DinethraDivanjana2001/TechBots-STM-based-Bot-Working/Raspberry Pi firmware/Edge detection/input_image.jpeg

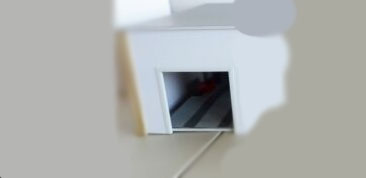
Raspberry Pi firmware/Edge detection/input_image.jpeg
