DinethraDivanjana2001/TechBots-STM-based-Bot-Working/3D designs/slrc 3D assembly blender/Assem1.STEP - Motor Assembly.STEP-1 65mm Wheel_默认.STEP-1 蓝色轮毂_默认.STEP-1.STL

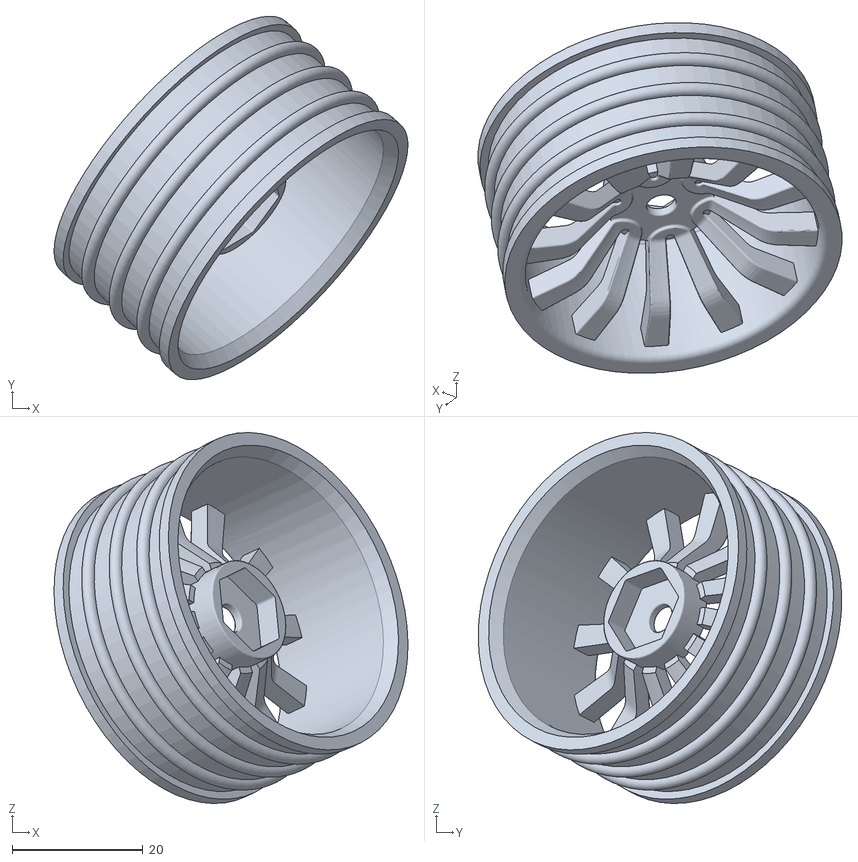
[picture p23: CAD file, 2024-07-25]
3D designs/slrc 3D assembly blender/Assem1.STEP - Motor Assembly.STEP-1 65mm Wheel_默认.STEP-1 蓝色轮毂_默认.STEP-1.STL
54.2 x 55.7 x 56.8
