DinethraDivanjana2001/TechBots-STM-based-Bot-Working/3D designs/slrc 3D assembly blender/Assem1.STEP - Motor Assembly.STEP-1 65mm Wheel_默认.STEP-1 3MM联轴器_默认.STEP-1.STL

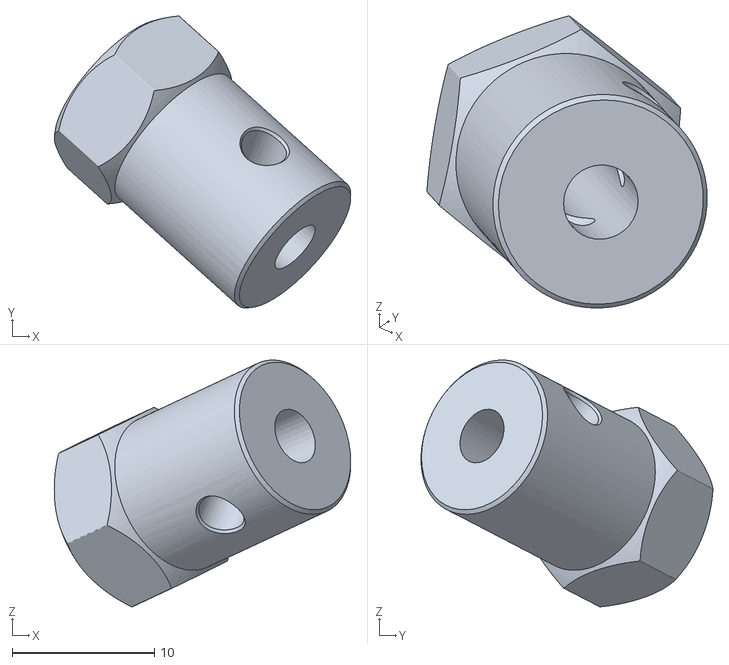
[picture p25: CAD file, 2024-07-25]
3D designs/slrc 3D assembly blender/Assem1.STEP - Motor Assembly.STEP-1 65mm Wheel_默认.STEP-1 3MM联轴器_默认.STEP-1.STL
20.9 x 20.6 x 17.4
