DinethraDivanjana2001/TechBots-STM-based-Bot-Working/3D designs/slrc 3D assembly blender/Assem1.STEP - Full  Arm Assembly.STEP-1 RDS3225 v7.STEP-2 RDS3225 v7_3^RDS3225 v7.STEP-1 RDS3225-0_3^RDS3225 v7_3_RDS3225 v7.STEP-1.STL

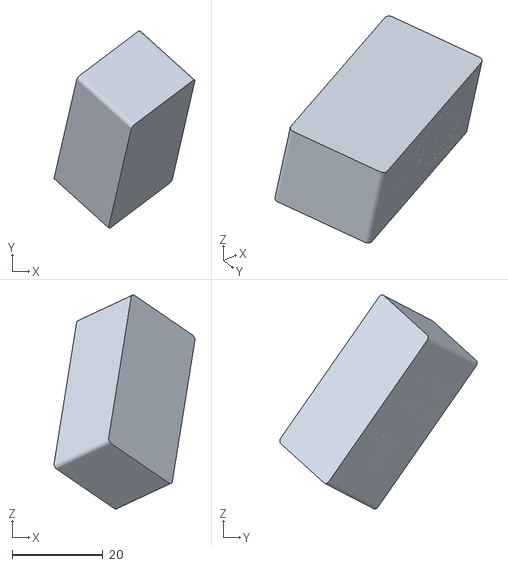
[picture p26: CAD file, 2024-07-25]
3D designs/slrc 3D assembly blender/Assem1.STEP - Full Arm Assembly.STEP-1 RDS3225 v7.STEP-2 RDS3225 v7_3^RDS3225 v7.STEP-1 RDS3225-0_3^RDS3225 v7_3_RDS3225 v7.STEP-1.STL
31.0 x 43.4 x 47.1
