DinethraDivanjana2001/TechBots-STM-based-Bot-Working/3D designs/slrc 3D assembly blender/Assem1.STEP - Full  Arm Assembly.STEP-1 Arm gripper new.STEP-2.STL

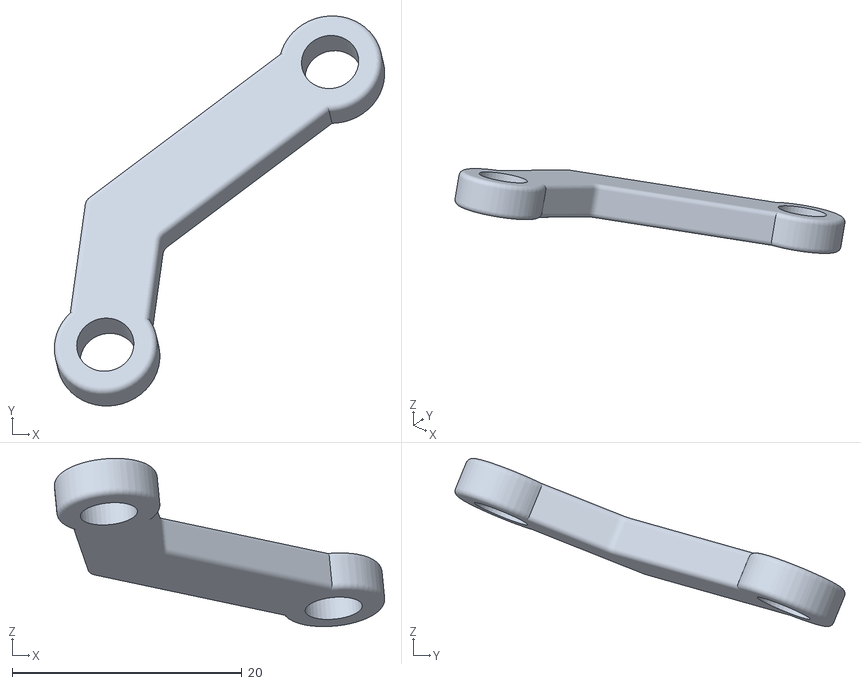
[picture p27: CAD file, 2024-07-25]
3D designs/slrc 3D assembly blender/Assem1.STEP - Full Arm Assembly.STEP-1 Arm gripper new.STEP-2.STL
28.7 x 33.9 x 14.6
