DinethraDivanjana2001/TechBots-STM-based-Bot-Working/3D designs/slrc 3D assembly blender/Assem1.STEP - Motor Assembly.STEP-1 metal-gearmotor-bracket.STEP-1.STL

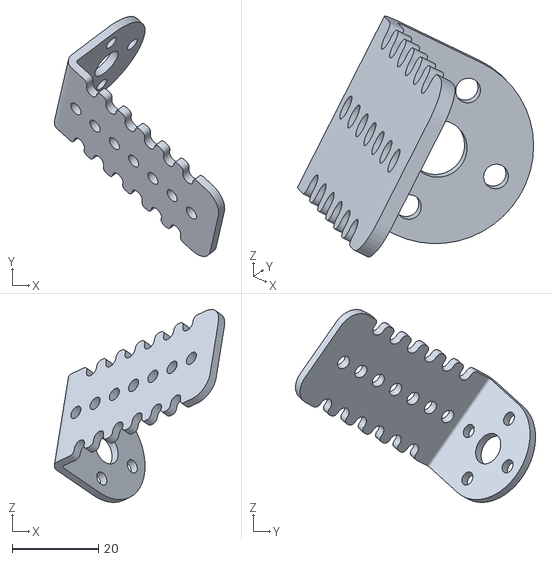
[picture p28: CAD file, 2024-07-25]
3D designs/slrc 3D assembly blender/Assem1.STEP - Motor Assembly.STEP-1 metal-gearmotor-bracket.STEP-1.STL
39.4 x 55.5 x 44.6
