DinethraDivanjana2001/TechBots-STM-based-Bot-Working/3D designs/slrc 3D assembly blender/Assem1.STEP - Motor Assembly.STEP-1 25d-metal-gearmotor-34-47-encoder.step.STEP-1 25d-metal-gearmotor-34-47-encoder2.step.STEP-1.STL

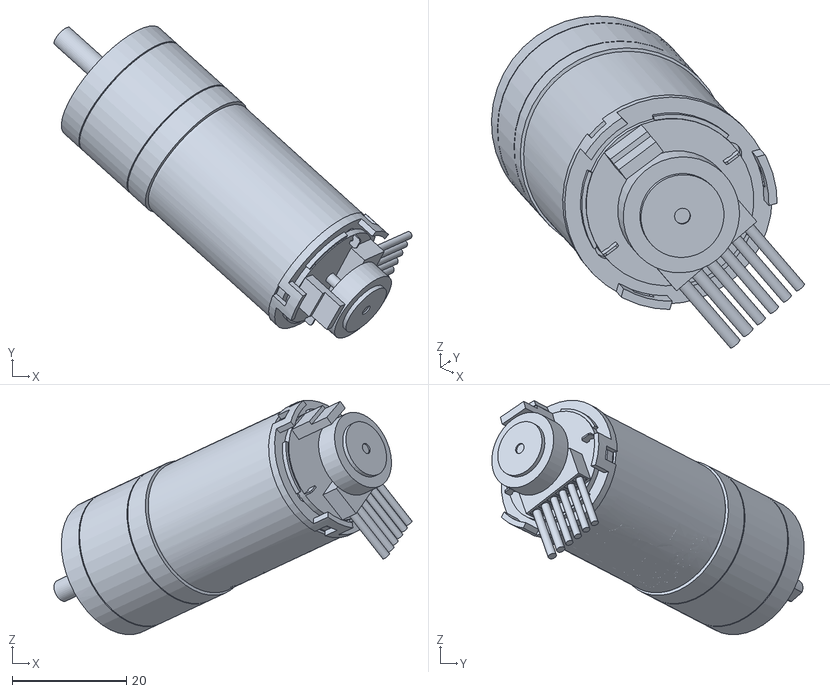
[picture p29: CAD file, 2024-07-25]
3D designs/slrc 3D assembly blender/Assem1.STEP - Motor Assembly.STEP-1 25d-metal-gearmotor-34-47-encoder.step.STEP-1 25d-metal-gearmotor-34-47-encoder2.step.STEP-1.STL
62.8 x 54.7 x 41.0
