DinethraDivanjana2001/TechBots-STM-based-Bot-Working/3D designs/slrc 3D assembly blender/Assem1.STEP - Tof assembly.STEP-1 vl53l0x.STEP-1 pin_header.STEP-6.STL

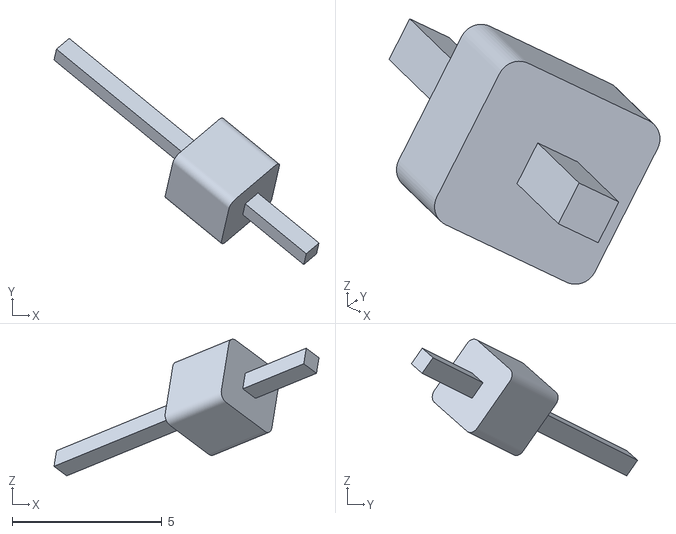
[picture p30: CAD file, 2024-07-25]
3D designs/slrc 3D assembly blender/Assem1.STEP - Tof assembly.STEP-1 vl53l0x.STEP-1 pin_header.STEP-6.STL
8.84 x 7.55 x 4.56
