DinethraDivanjana2001/TechBots-STM-based-Bot-Working/3D designs/slrc 3D assembly blender/Assem1.STEP - Tof assembly.STEP-1 vl53l0x.STEP-1 vl53l0x_PCB.STEP-1.STL

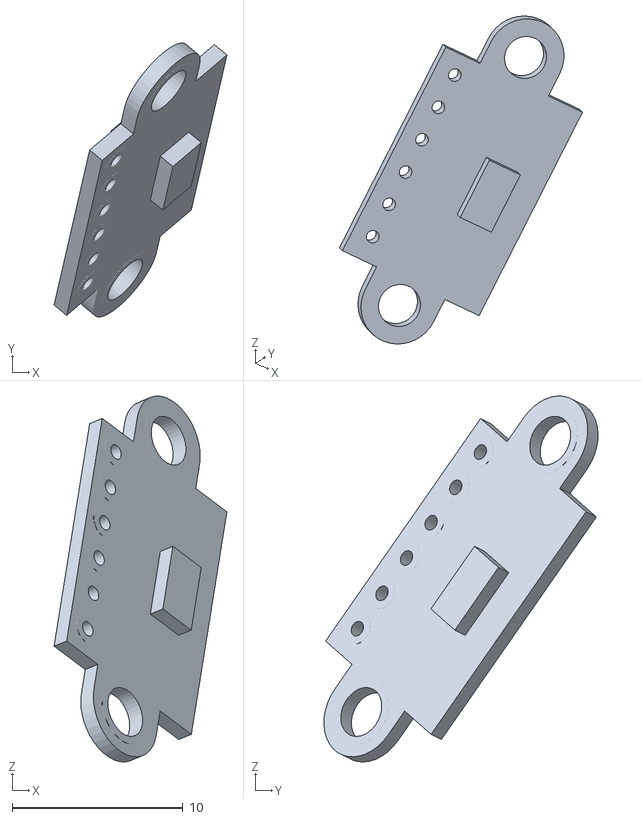
[picture p31: CAD file, 2024-07-25]
3D designs/slrc 3D assembly blender/Assem1.STEP - Tof assembly.STEP-1 vl53l0x.STEP-1 vl53l0x_PCB.STEP-1.STL
10.1 x 16.0 x 21.4
