DinethraDivanjana2001/TechBots-STM-based-Bot-Working/3D designs/slrc 3D assembly blender/Assem1.STEP - Full  Arm Assembly.STEP-1 RDS3225 v7.STEP-1 RDS3225 v7_3^RDS3225 v7.STEP-1 RDS3225-1_3^RDS3225 v7_3_RDS3225 v7.STEP-1.STL

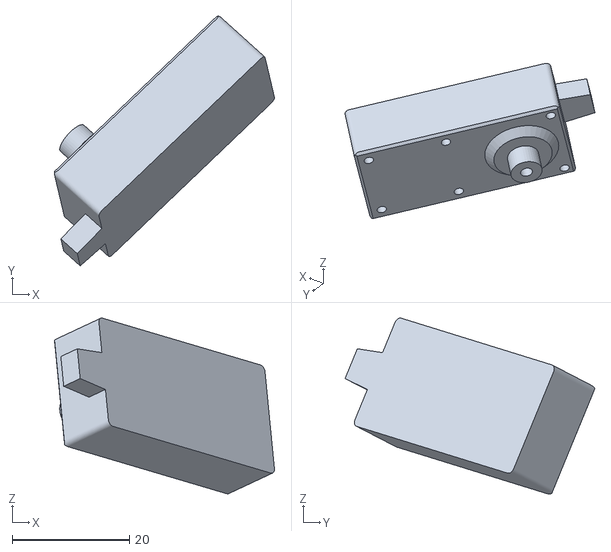
[picture p34: CAD file, 2024-07-25]
3D designs/slrc 3D assembly blender/Assem1.STEP - Full Arm Assembly.STEP-1 RDS3225 v7.STEP-1 RDS3225 v7_3^RDS3225 v7.STEP-1 RDS3225-1_3^RDS3225 v7_3_RDS3225 v7.STEP-1.STL
37.5 x 42.5 x 29.9
