DinethraDivanjana2001/TechBots-STM-based-Bot-Working/3D designs/slrc 3D assembly blender/Assem1.STEP - Full  Arm Assembly.STEP-1 RDS3225 v7.STEP-1 RDS3225 v7_3^RDS3225 v7.STEP-1 RDS3225-0_3^RDS3225 v7_3_RDS3225 v7.STEP-1.STL

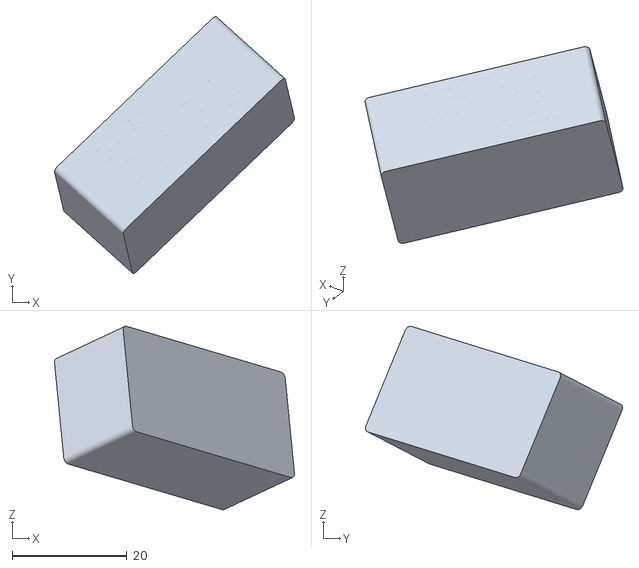
[picture p35: CAD file, 2024-07-25]
3D designs/slrc 3D assembly blender/Assem1.STEP - Full Arm Assembly.STEP-1 RDS3225 v7.STEP-1 RDS3225 v7_3^RDS3225 v7.STEP-1 RDS3225-0_3^RDS3225 v7_3_RDS3225 v7.STEP-1.STL
41.9 x 44.9 x 32.0
