DinethraDivanjana2001/TechBots-STM-based-Bot-Working/3D designs/slrc 3D assembly blender/Assem1.STEP - Tof assembly.STEP-2 New tof mount.STEP-1.STL

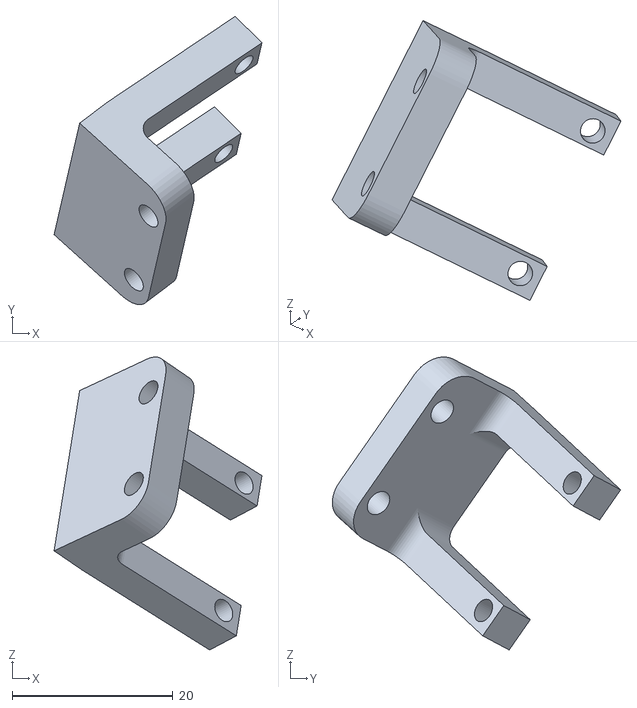
[picture p38: CAD file, 2024-07-25]
3D designs/slrc 3D assembly blender/Assem1.STEP - Tof assembly.STEP-2 New tof mount.STEP-1.STL
25.9 x 35.9 x 36.5
