DinethraDivanjana2001/TechBots-STM-based-Bot-Working/3D designs/slrc 3D assembly blender/Assem1.STEP - Full  Arm Assembly.STEP-1 proximity tl-w5mc1_Valor predeterminado.STEP-1.STL

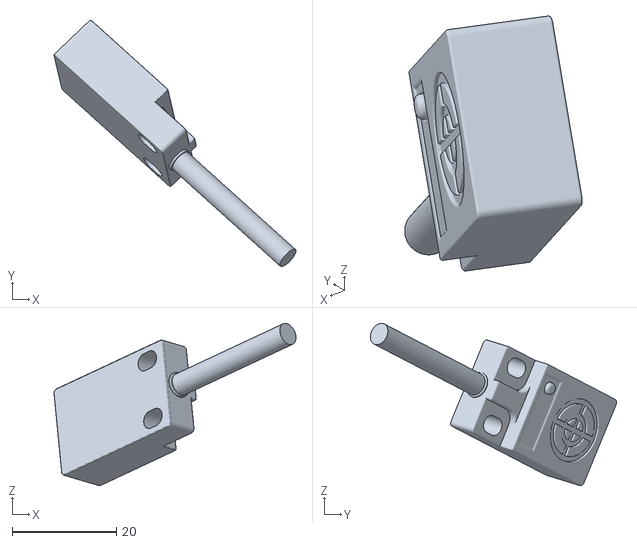
[picture p40: CAD file, 2024-07-25]
3D designs/slrc 3D assembly blender/Assem1.STEP - Full Arm Assembly.STEP-1 proximity tl-w5mc1_Valor predeterminado.STEP-1.STL
46.5 x 47.3 x 31.2
