DinethraDivanjana2001/TechBots-STM-based-Bot-Working/3D designs/slrc 3D assembly blender/Assem1.STEP - Full  Arm Assembly.STEP-1 Jaw plate flip new.STEP-1.STL

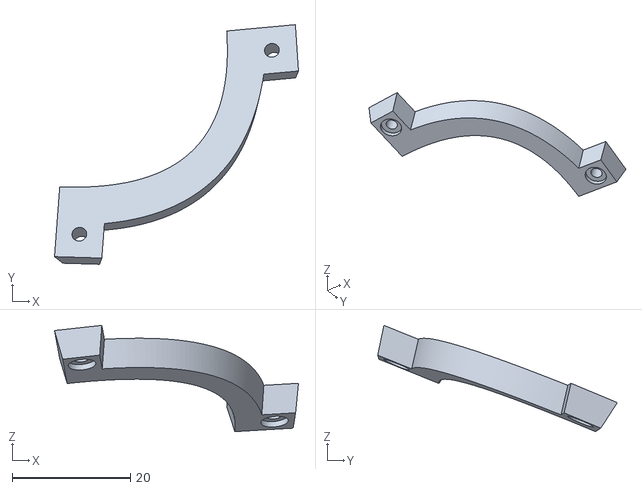
[picture p42: CAD file, 2024-07-25]
3D designs/slrc 3D assembly blender/Assem1.STEP - Full Arm Assembly.STEP-1 Jaw plate flip new.STEP-1.STL
41.2 x 40.5 x 18.0
