DinethraDivanjana2001/TechBots-STM-based-Bot-Working/3D designs/slrc 3D assembly blender/Assem1.STEP - Motor Assembly.STEP-2 metal-gearmotor-bracket.STEP-1.STL

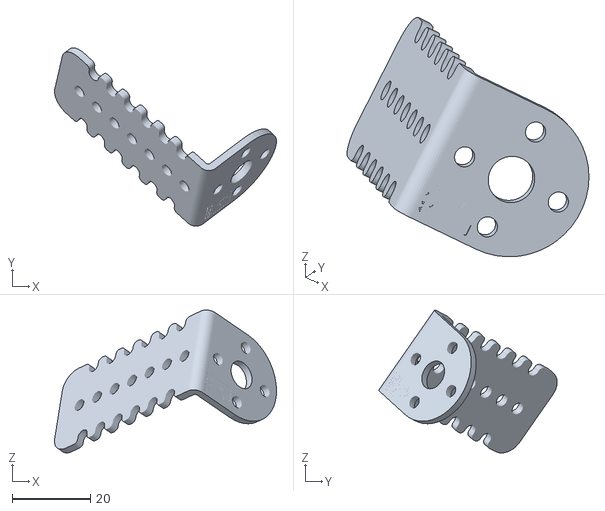
[picture p45: CAD file, 2024-07-25]
3D designs/slrc 3D assembly blender/Assem1.STEP - Motor Assembly.STEP-2 metal-gearmotor-bracket.STEP-1.STL
56.6 x 45.4 x 36.4
