DinethraDivanjana2001/TechBots-STM-based-Bot-Working/3D designs/slrc 3D assembly blender/Assem1.STEP - Motor Assembly.STEP-2 25d-metal-gearmotor-34-47-encoder.step.STEP-1 25d-metal-gearmotor-34-47-encoder2.step.STEP-1.STL

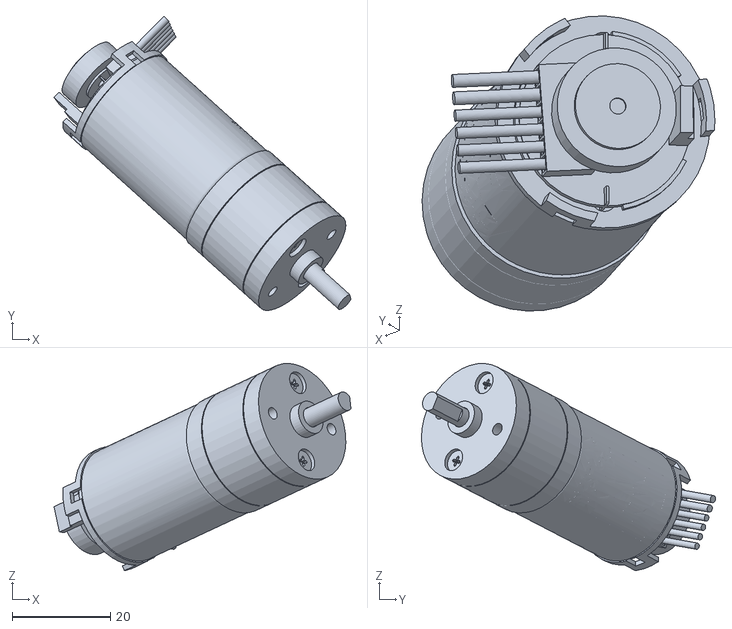
[picture p47: CAD file, 2024-07-25]
3D designs/slrc 3D assembly blender/Assem1.STEP - Motor Assembly.STEP-2 25d-metal-gearmotor-34-47-encoder.step.STEP-1 25d-metal-gearmotor-34-47-encoder2.step.STEP-1.STL
60.6 x 60.0 x 42.3
