DinethraDivanjana2001/TechBots-STM-based-Bot-Working/3D designs/slrc 3D assembly blender/Assem1.STEP - Motor Assembly.STEP-2 25d-metal-gearmotor-34-47-encoder.step.STEP-1 25d-metal-gearmotor-34-47-encoder1.step.STEP-1.STL

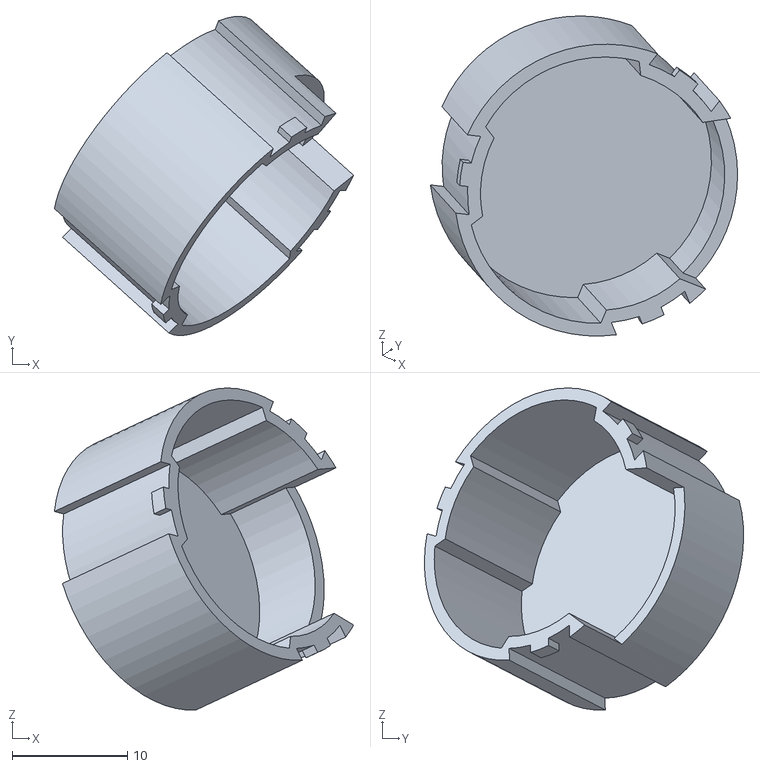
[picture p48: CAD file, 2024-07-25]
3D designs/slrc 3D assembly blender/Assem1.STEP - Motor Assembly.STEP-2 25d-metal-gearmotor-34-47-encoder.step.STEP-1 25d-metal-gearmotor-34-47-encoder1.step.STEP-1.STL
25.9 x 27.7 x 27.9
