DinethraDivanjana2001/TechBots-STM-based-Bot-Working/3D designs/slrc 3D assembly blender/Assem1.STEP - Motor Assembly.STEP-1 25d-metal-gearmotor-34-47-encoder.step.STEP-1 25d-metal-gearmotor-34-47-encoder1.step.STEP-1.STL

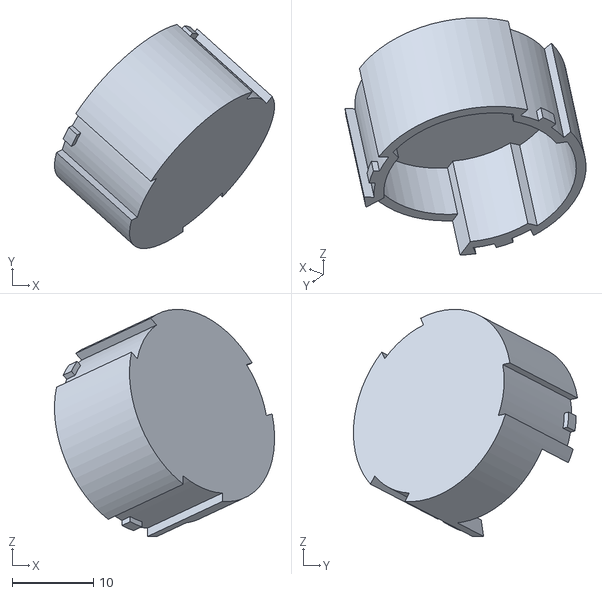
[picture p49: CAD file, 2024-07-25]
3D designs/slrc 3D assembly blender/Assem1.STEP - Motor Assembly.STEP-1 25d-metal-gearmotor-34-47-encoder.step.STEP-1 25d-metal-gearmotor-34-47-encoder1.step.STEP-1.STL
27.0 x 27.5 x 27.9
