DinethraDivanjana2001/TechBots-STM-based-Bot-Working/3D designs/slrc 3D assembly blender/Assem1.STEP - vl53l0x.STEP-2 pin_header.STEP-4.STL

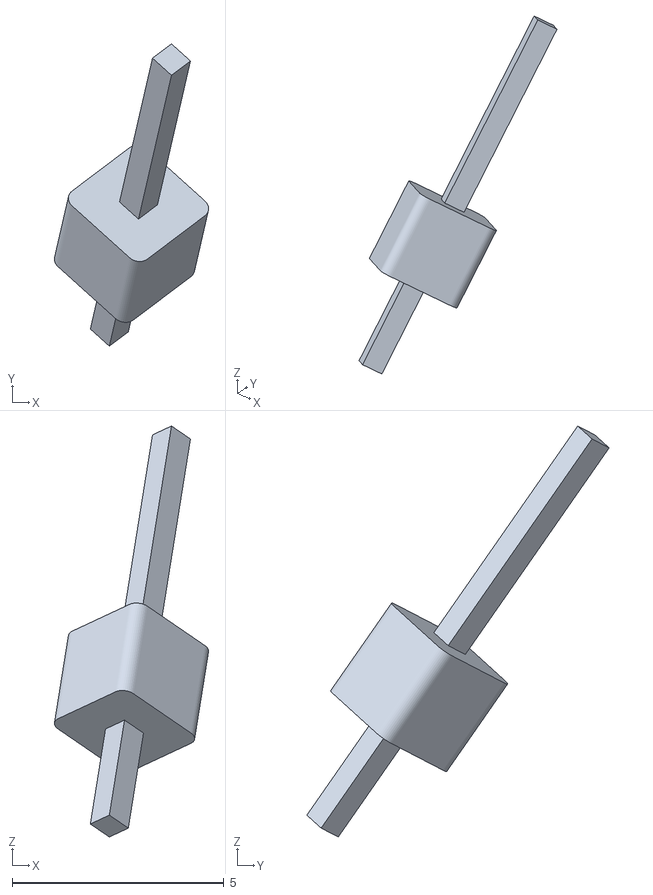
[picture p52: CAD file, 2024-07-25]
3D designs/slrc 3D assembly blender/Assem1.STEP - vl53l0x.STEP-2 pin_header.STEP-4.STL
3.65 x 7.14 x 9.71
