DinethraDivanjana2001/TechBots-STM-based-Bot-Working/Shooter/Solid_works_design/Wheel.SLDPRT

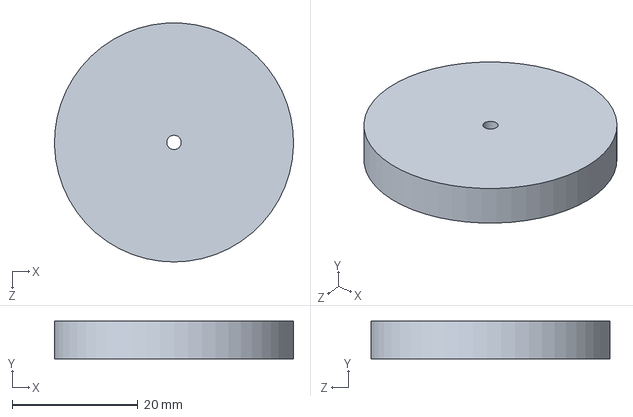
[picture p53: CAD file, 2024-07-25]
Shooter/Solid_works_design/Wheel.SLDPRT
38.0 x 6.00 x 38.0 mm
