DinethraDivanjana2001/TechBots-STM-based-Bot-Working/Shooter/Solid_works_design/rs380 motor.step.SLDPRT

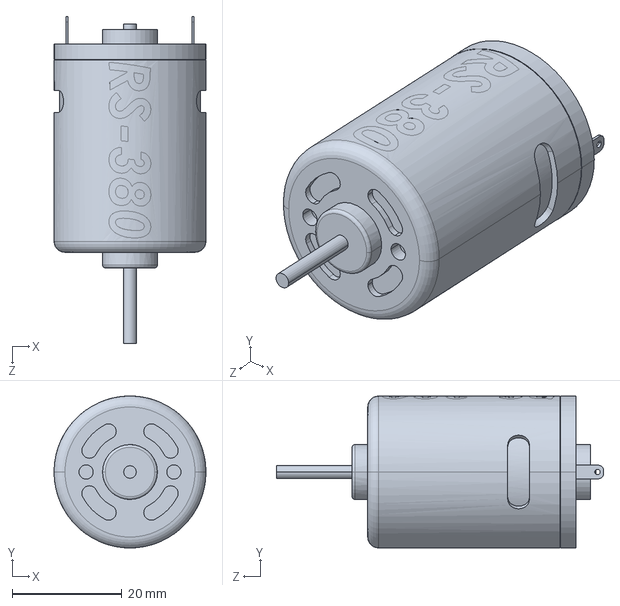
[picture p54: CAD file, 2024-07-25]
Shooter/Solid_works_design/rs380 motor.step.SLDPRT
27.7 x 27.7 x 59.7 mm
