DinethraDivanjana2001/TechBots-STM-based-Bot-Working/Shooter/Solid_works_design/Shooter.SLDPRT

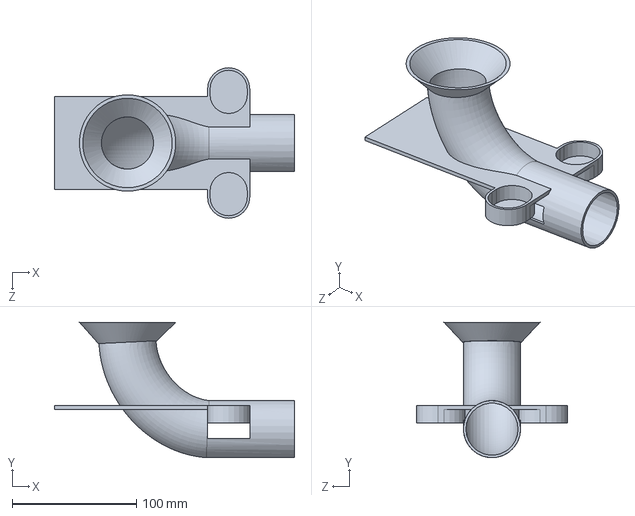
[picture p55: CAD file, 2024-07-25]
Shooter/Solid_works_design/Shooter.SLDPRT
193.2 x 109.0 x 121.2 mm
