DinethraDivanjana2001/TechBots-STM-based-Bot-Working/3D designs/slrc 3D assembly blender/Assem1.STEP - caster ball wheel.STEP-1.STL

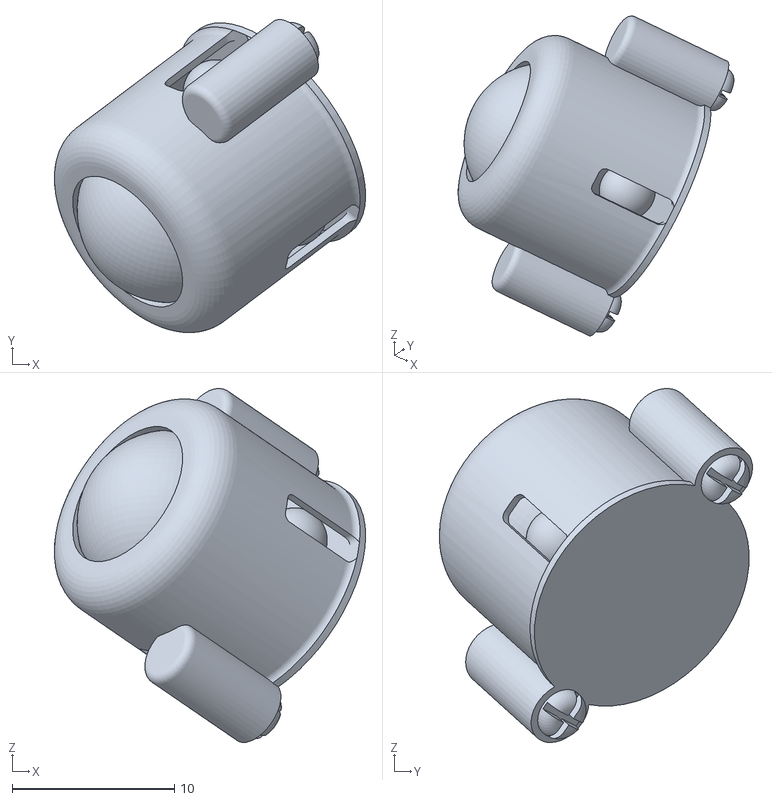
[picture p56: CAD file, 2024-07-25]
3D designs/slrc 3D assembly blender/Assem1.STEP - caster ball wheel.STEP-1.STL
19.2 x 19.3 x 21.8
