DinethraDivanjana2001/TechBots-STM-based-Bot-Working/3D designs/slrc 3D assembly blender/Assem1.STEP - Base.STEP-1.STL

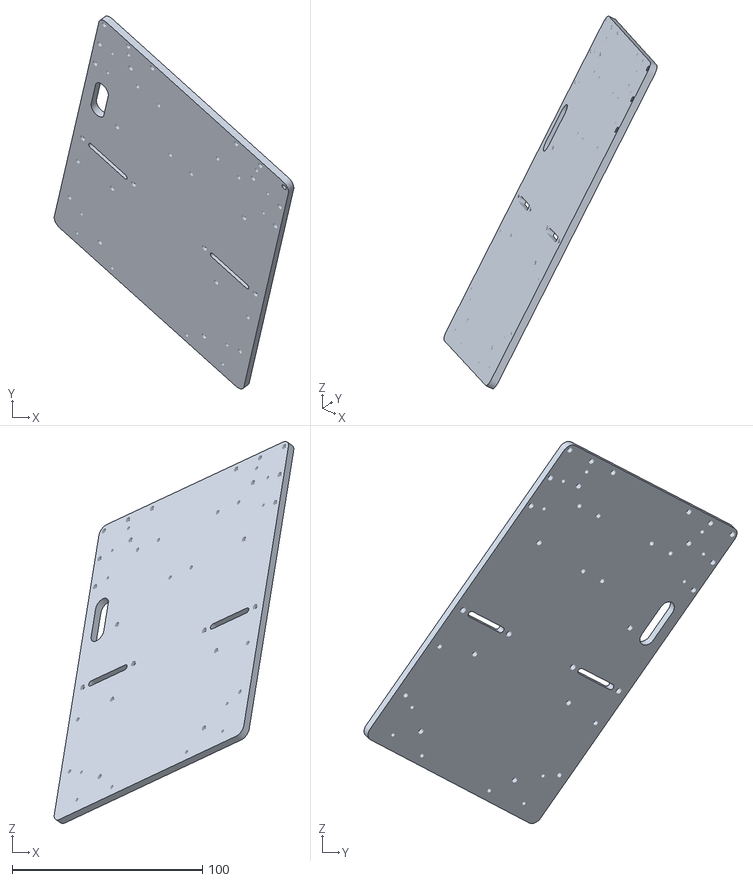
[picture p57: CAD file, 2024-07-25]
3D designs/slrc 3D assembly blender/Assem1.STEP - Base.STEP-1.STL
126.0 x 196.1 x 200.8
