DinethraDivanjana2001/TechBots-STM-based-Bot-Working/3D designs/slrc 3D assembly blender/Assem1.STEP - TCS34725 RGB sensor.step.STEP-1.STL

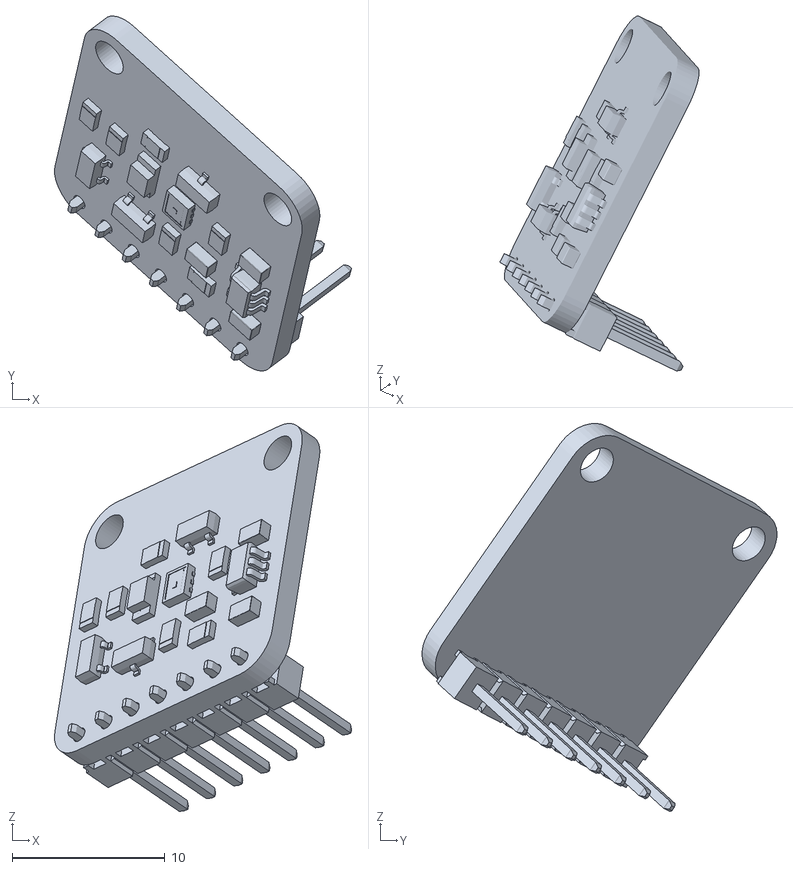
[picture p58: CAD file, 2024-07-25]
3D designs/slrc 3D assembly blender/Assem1.STEP - TCS34725 RGB sensor.step.STEP-1.STL
19.5 x 23.3 x 25.4
