DinethraDivanjana2001/TechBots-STM-based-Bot-Working/3D designs/slrc 3D assembly blender/Assem1.STEP - TFF-M3x8_DR113.step.STEP-3.STL

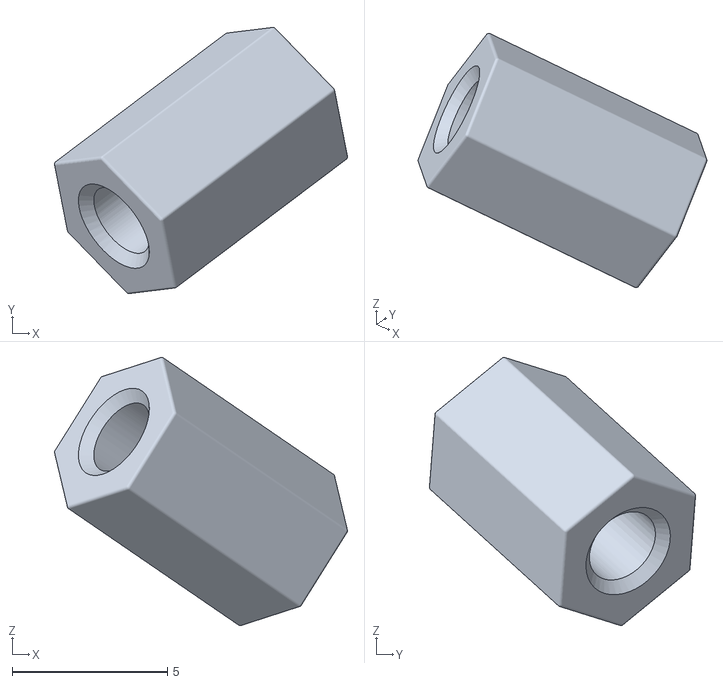
[picture p59: CAD file, 2024-07-25]
3D designs/slrc 3D assembly blender/Assem1.STEP - TFF-M3x8_DR113.step.STEP-3.STL
9.43 x 8.56 x 8.63
