DinethraDivanjana2001/TechBots-STM-based-Bot-Working/3D designs/slrc 3D assembly blender/Assem1.STEP - Stand Off 35mm_1.stp.STEP-1.STL

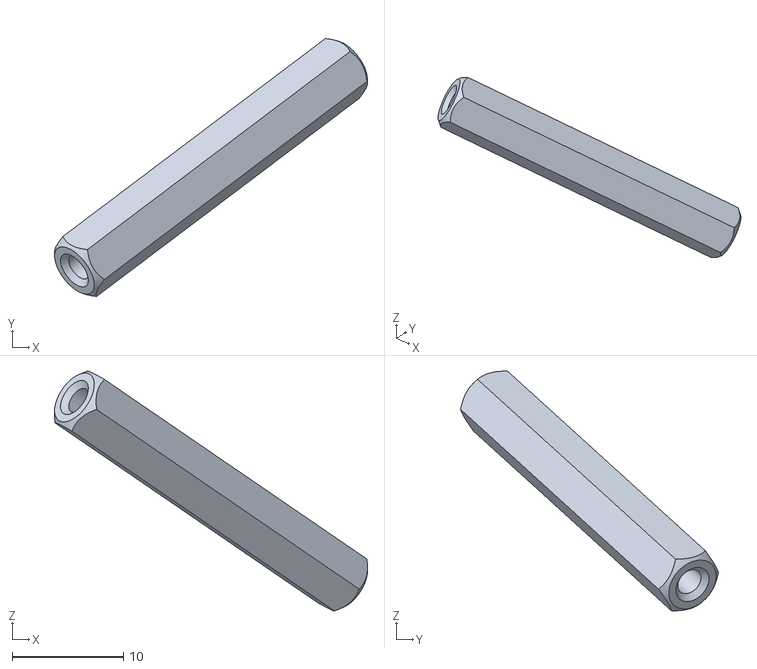
[picture p60: CAD file, 2024-07-25]
3D designs/slrc 3D assembly blender/Assem1.STEP - Stand Off 35mm_1.stp.STEP-1.STL
28.1 x 23.2 x 21.5
