DinethraDivanjana2001/TechBots-STM-based-Bot-Working/3D designs/slrc 3D assembly blender/Assem1.STEP - Turnigy_2200mAh_3S_20C_Lipo_Pack_Valor predeterminado.STEP-1.STL

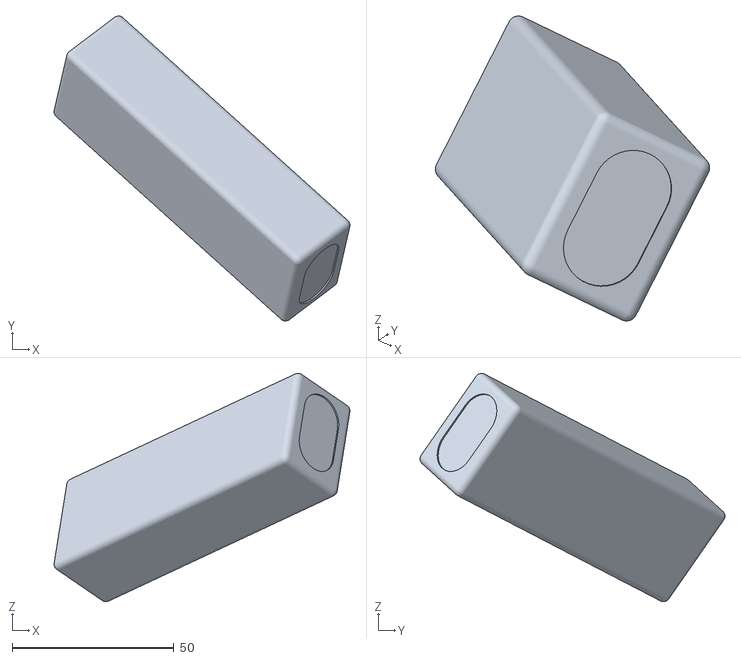
[picture p61: CAD file, 2024-07-25]
3D designs/slrc 3D assembly blender/Assem1.STEP - Turnigy_2200mAh_3S_20C_Lipo_Pack_Valor predeterminado.STEP-1.STL
91.4 x 94.2 x 70.5
