DinethraDivanjana2001/TechBots-STM-based-Bot-Working/3D designs/slrc 3D assembly blender/Assem1.STEP - TFF-M3x8_DR113.step.STEP-2.STL

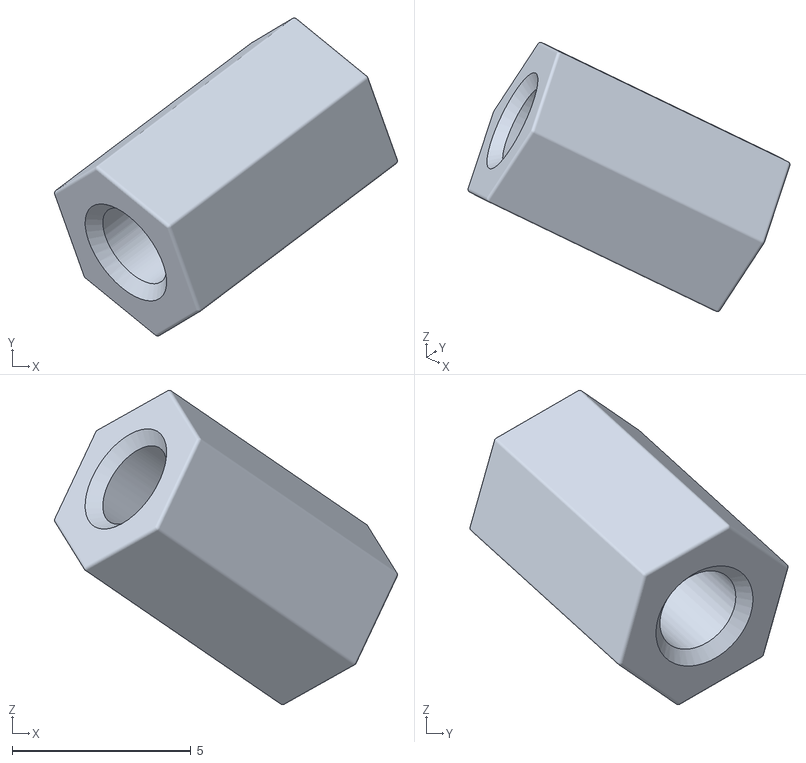
[picture p62: CAD file, 2024-07-25]
3D designs/slrc 3D assembly blender/Assem1.STEP - TFF-M3x8_DR113.step.STEP-2.STL
9.60 x 8.90 x 8.80
