DinethraDivanjana2001/TechBots-STM-based-Bot-Working/3D designs/slrc 3D assembly blender/Assem1.STEP - vl53l0x.STEP-2 vl53l0x_PCB.STEP-1.STL

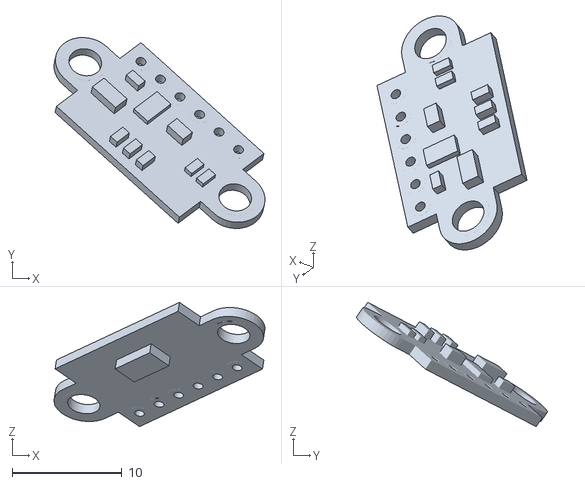
[picture p63: CAD file, 2024-07-25]
3D designs/slrc 3D assembly blender/Assem1.STEP - vl53l0x.STEP-2 vl53l0x_PCB.STEP-1.STL
19.3 x 17.4 x 11.3
