DinethraDivanjana2001/TechBots-STM-based-Bot-Working/3D designs/slrc 3D assembly blender/Assem1.STEP - rs380 motor_1.step.STEP-1 rs380 motor1_1.STEP.STEP-1.STL

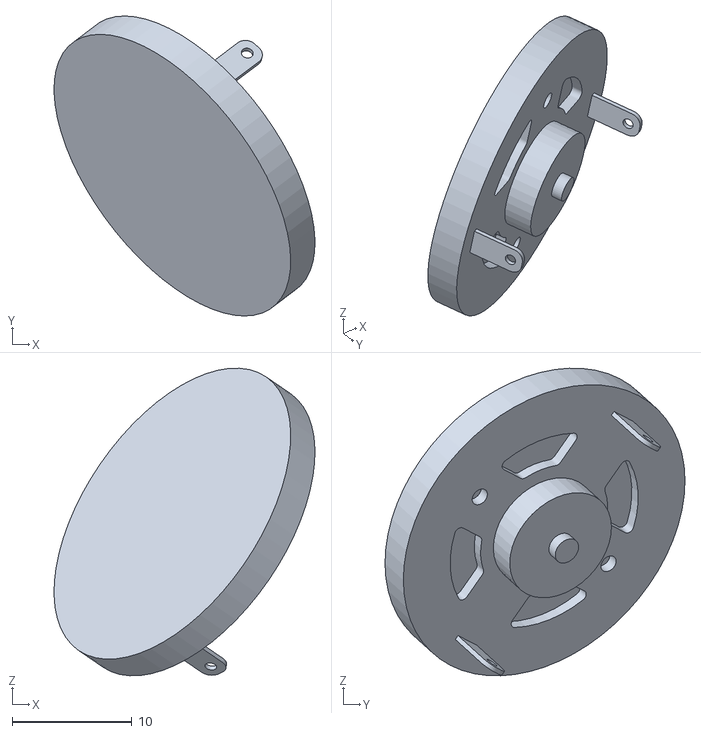
[picture p65: CAD file, 2024-07-25]
3D designs/slrc 3D assembly blender/Assem1.STEP - rs380 motor_1.step.STEP-1 rs380 motor1_1.STEP.STEP-1.STL
21.8 x 25.1 x 25.7
