DinethraDivanjana2001/TechBots-STM-based-Bot-Working/3D designs/slrc 3D assembly blender/Assem1.STEP - Even newer spacer.STEP-2.STL

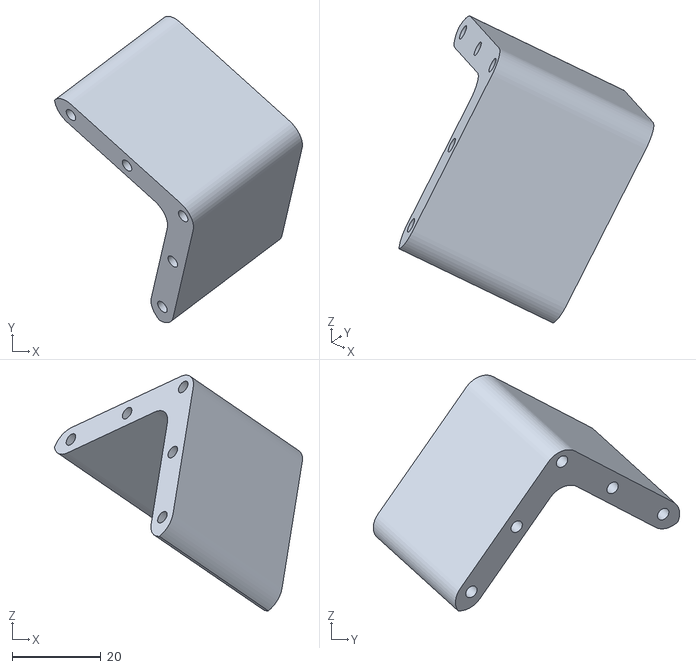
[picture p66: CAD file, 2024-07-25]
3D designs/slrc 3D assembly blender/Assem1.STEP - Even newer spacer.STEP-2.STL
55.8 x 68.9 x 53.0
