DinethraDivanjana2001/TechBots-STM-based-Bot-Working/3D designs/slrc 3D assembly blender/Assem1.STEP - New Shooter.STEP-1 Left Shooter.STEP-1.STL

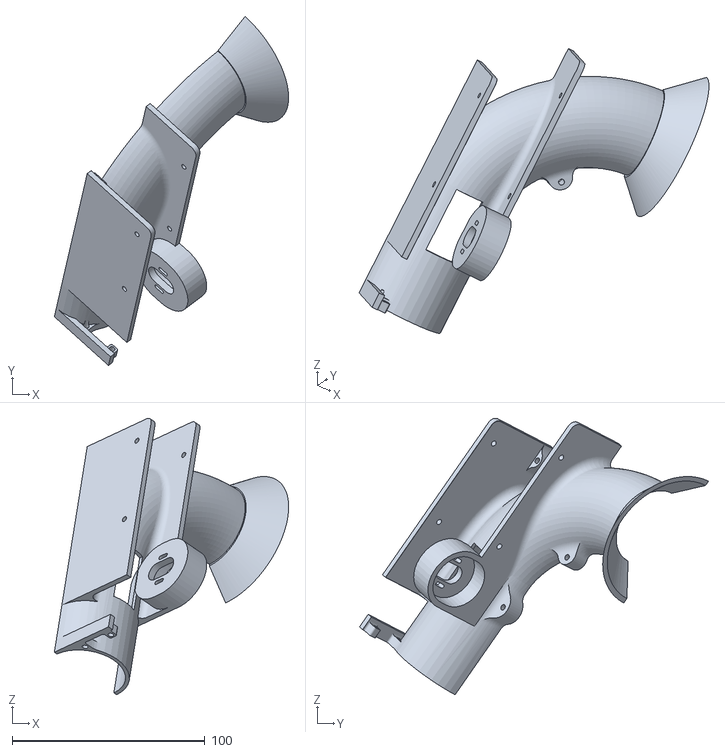
[picture p67: CAD file, 2024-07-25]
3D designs/slrc 3D assembly blender/Assem1.STEP - New Shooter.STEP-1 Left Shooter.STEP-1.STL
121.5 x 181.0 x 143.4
