DinethraDivanjana2001/TechBots-STM-based-Bot-Working/3D designs/slrc 3D assembly blender/Assem1.STEP - Top Base Plate.STEP-1.STL

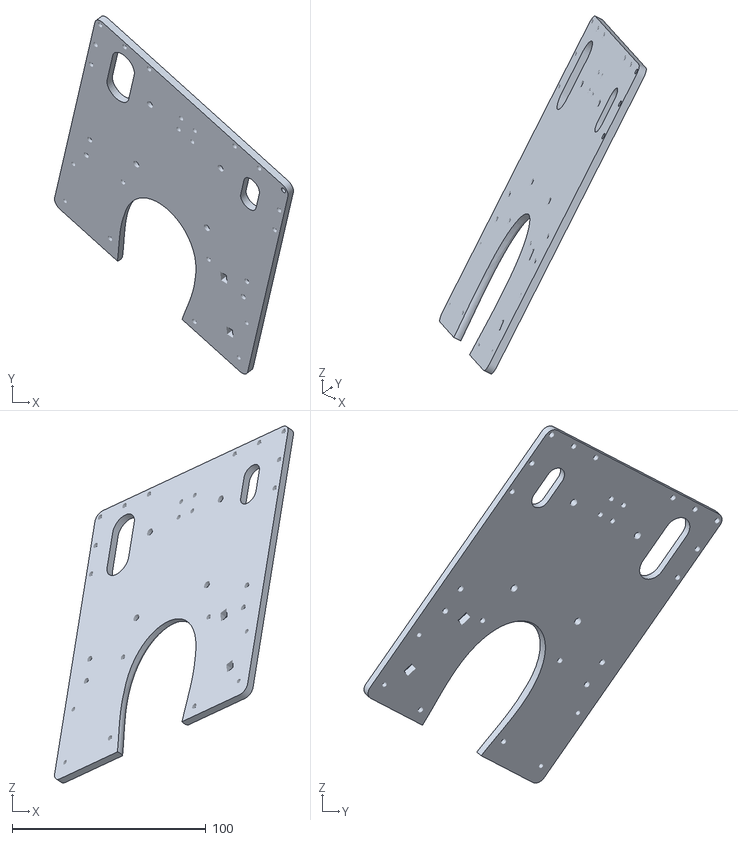
[picture p68: CAD file, 2024-07-25]
3D designs/slrc 3D assembly blender/Assem1.STEP - Top Base Plate.STEP-1.STL
123.3 x 184.7 x 184.2
