DinethraDivanjana2001/TechBots-STM-based-Bot-Working/3D designs/slrc 3D assembly blender/Assem1.STEP - rs380 motor.step.STEP-1 rs380 motor2.STEP.STEP-1.STL

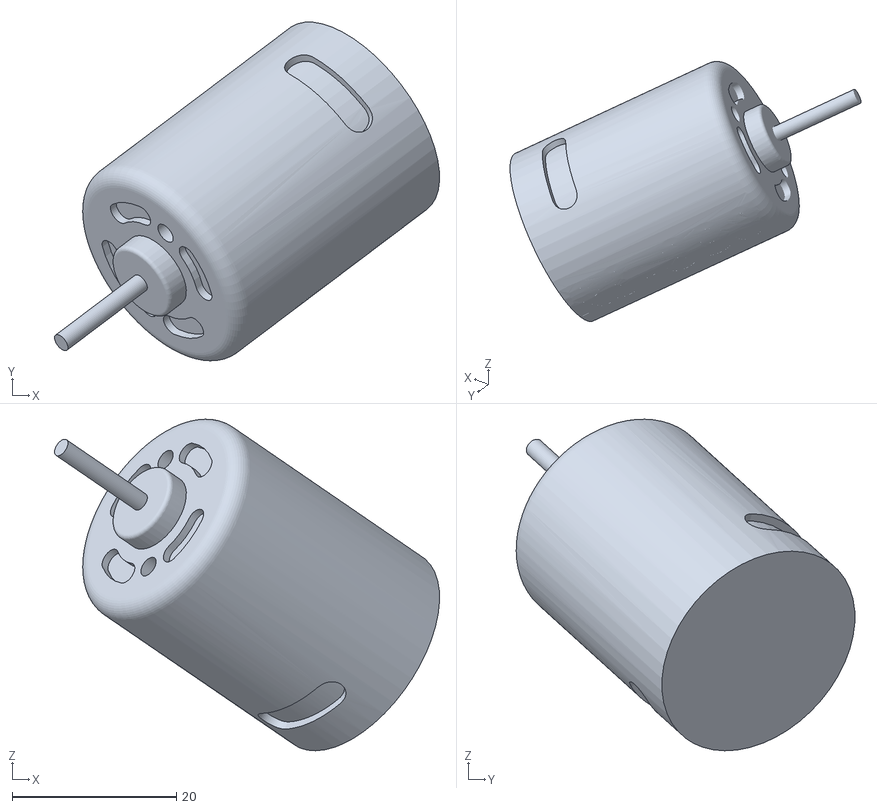
[picture p69: CAD file, 2024-07-25]
3D designs/slrc 3D assembly blender/Assem1.STEP - rs380 motor.step.STEP-1 rs380 motor2.STEP.STEP-1.STL
46.9 x 41.2 x 40.4
