DinethraDivanjana2001/TechBots-STM-based-Bot-Working/3D designs/slrc 3D assembly blender/Assem1.STEP - qtrx-hd-25x.step.STEP-1.STL

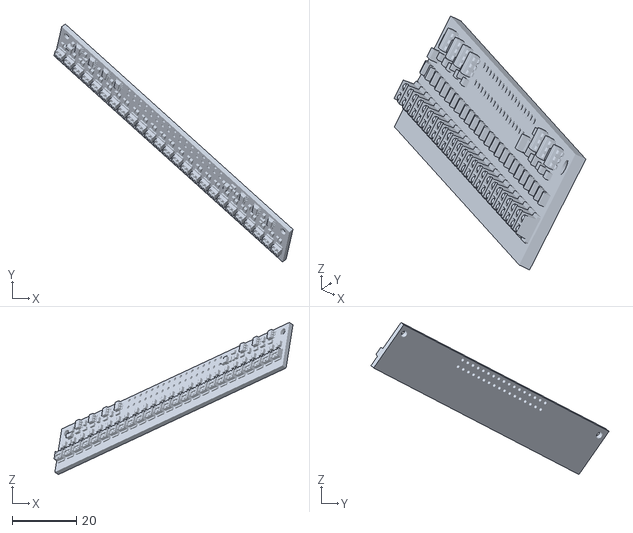
[picture p70: CAD file, 2024-07-25]
3D designs/slrc 3D assembly blender/Assem1.STEP - qtrx-hd-25x.step.STEP-1.STL
74.4 x 74.1 x 47.3
