DinethraDivanjana2001/TechBots-STM-based-Bot-Working/3D designs/slrc 3D assembly blender/Assem1.STEP - TFF-M3x8_DR113.step.STEP-4.STL

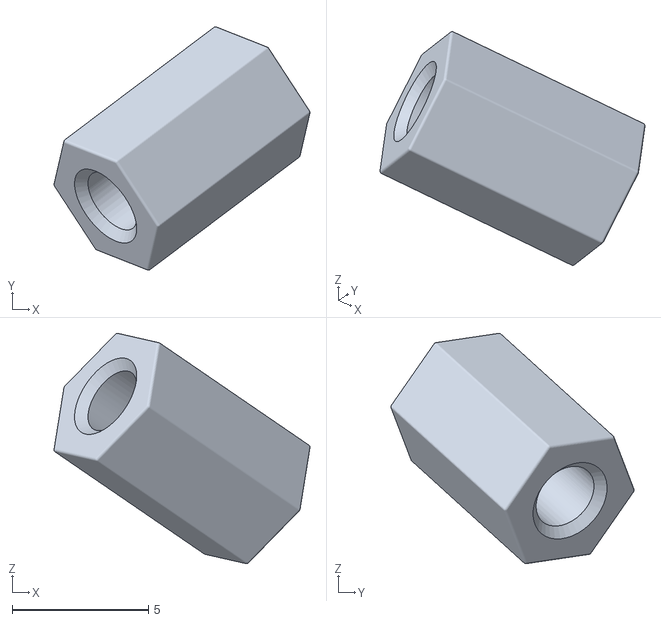
[picture p71: CAD file, 2024-07-25]
3D designs/slrc 3D assembly blender/Assem1.STEP - TFF-M3x8_DR113.step.STEP-4.STL
9.39 x 8.93 x 8.45
