DinethraDivanjana2001/TechBots-STM-based-Bot-Working/3D designs/slrc 3D assembly blender/Assem1.STEP - Even newer spacer.STEP-1.STL

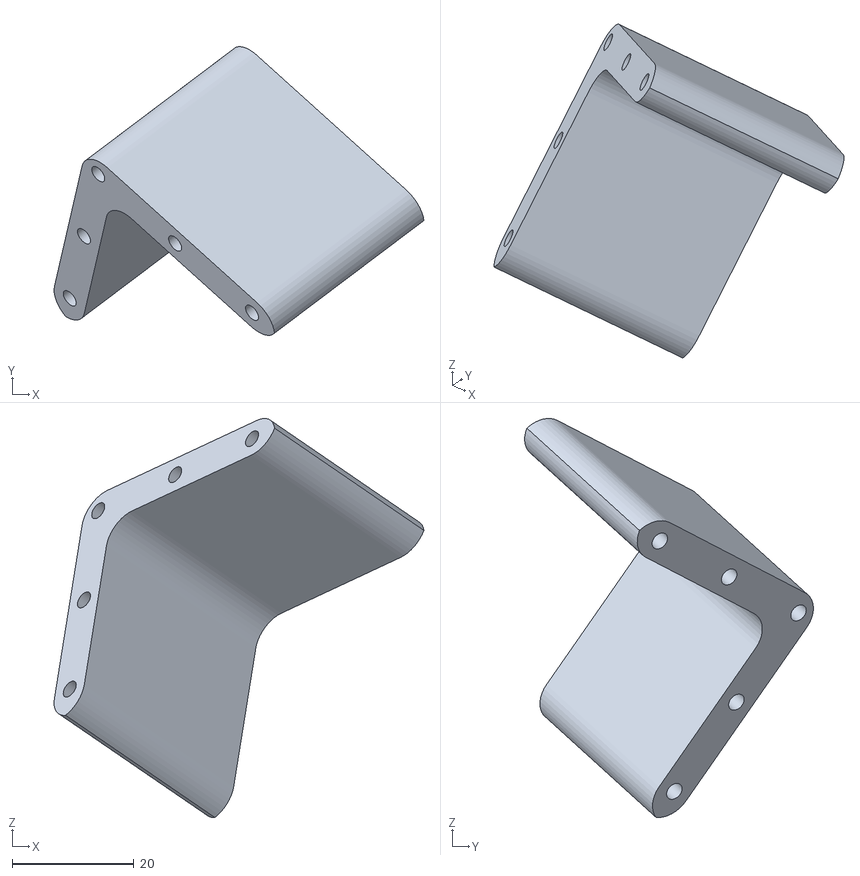
[picture p72: CAD file, 2024-07-25]
3D designs/slrc 3D assembly blender/Assem1.STEP - Even newer spacer.STEP-1.STL
60.7 x 47.4 x 65.5
