DinethraDivanjana2001/TechBots-STM-based-Bot-Working/3D designs/slrc 3D assembly blender/Assem1.STEP - New Shooter.STEP-1 Right Shooter.STEP-1.STL

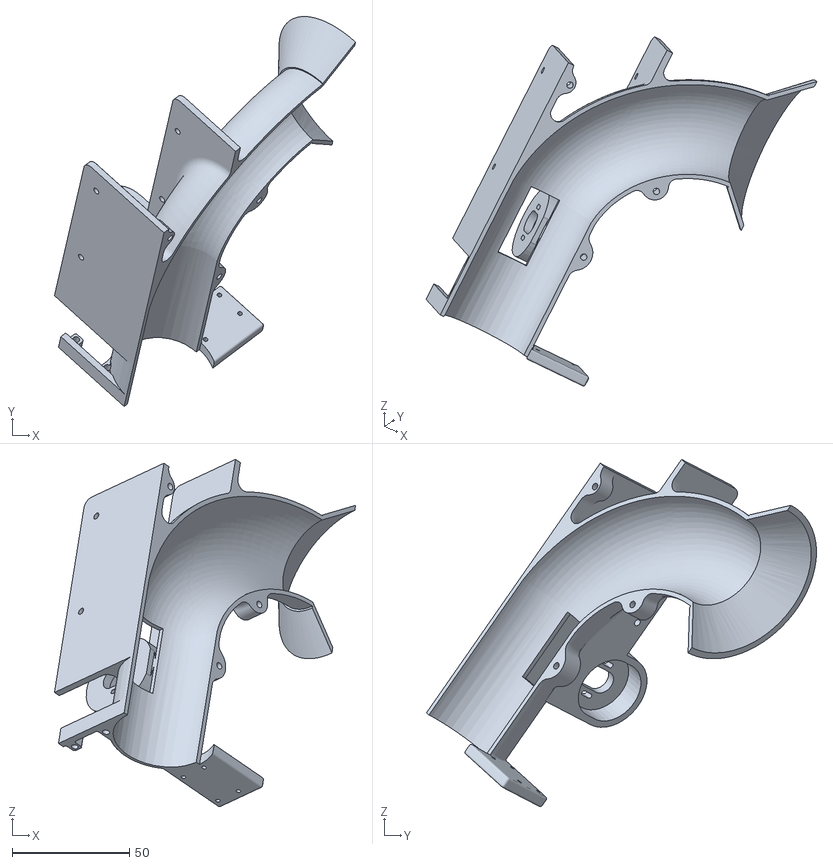
[picture p73: CAD file, 2024-07-25]
3D designs/slrc 3D assembly blender/Assem1.STEP - New Shooter.STEP-1 Right Shooter.STEP-1.STL
128.6 x 166.6 x 148.4
