DinethraDivanjana2001/TechBots-STM-based-Bot-Working/3D designs/slrc 3D assembly blender/Assem1.STEP - Rpi Holder.STEP-1.STL

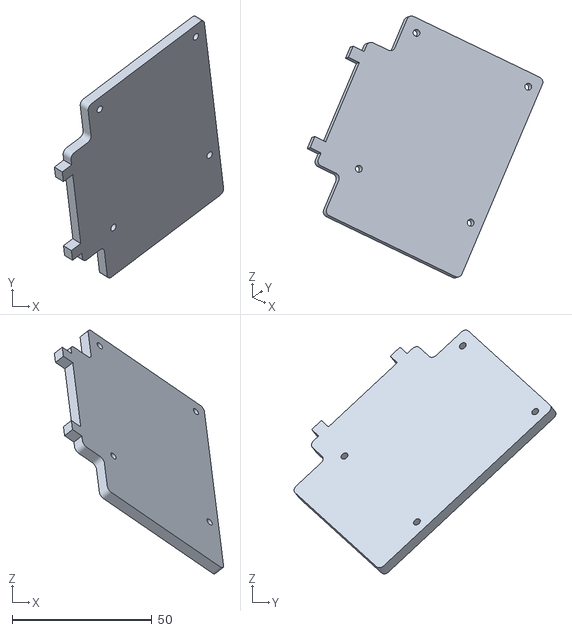
[picture p74: CAD file, 2024-07-25]
3D designs/slrc 3D assembly blender/Assem1.STEP - Rpi Holder.STEP-1.STL
60.5 x 93.6 x 87.1
