DinethraDivanjana2001/TechBots-STM-based-Bot-Working/3D designs/slrc 3D assembly blender/Assem1.STEP - qtrx-hd-15x.step.STEP-1.STL

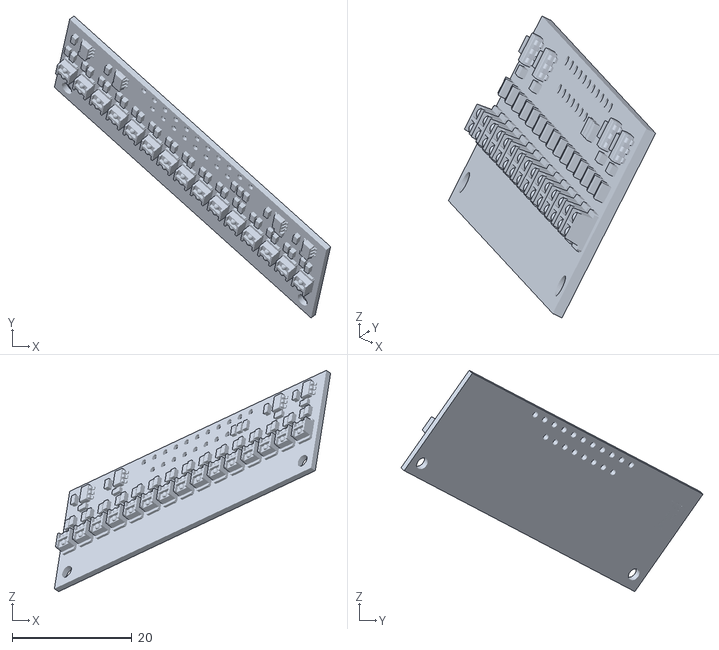
[picture p75: CAD file, 2024-07-25]
3D designs/slrc 3D assembly blender/Assem1.STEP - qtrx-hd-15x.step.STEP-1.STL
46.1 x 50.4 x 36.9
