DinethraDivanjana2001/TechBots-STM-based-Bot-Working/3D designs/slrc 3D assembly blender/Assem1.STEP - TFF-M3x8_DR113.step.STEP-1.STL

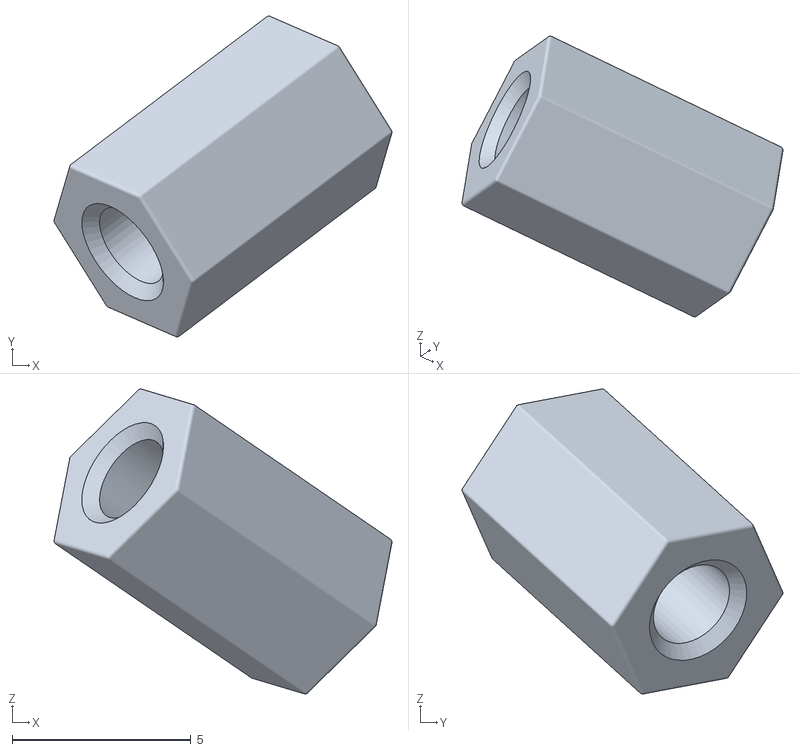
[picture p76: CAD file, 2024-07-25]
3D designs/slrc 3D assembly blender/Assem1.STEP - TFF-M3x8_DR113.step.STEP-1.STL
9.44 x 8.96 x 8.52
