DinethraDivanjana2001/TechBots-STM-based-Bot-Working/3D designs/3D Renders/Arm Assembly.png

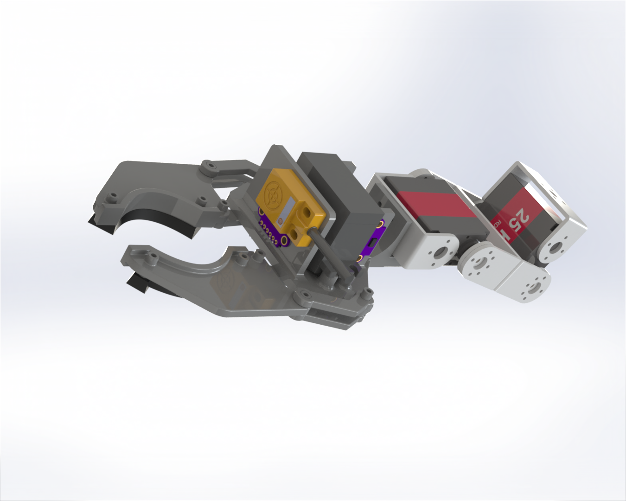
3D designs/3D Renders/Arm Assembly.png
