DinethraDivanjana2001/TechBots-STM-based-Bot-Working/firmware/PID-Basic_tested_varification failed(motor issue)/Core/Src/main.c

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
/* Includes ------------------------------------------------------------------*/
#include "main.h"

/* USER CODE BEGIN Includes */
#include <stdio.h>

/* USER CODE END Includes */

ADC_HandleTypeDef hadc1;

I2C_HandleTypeDef hi2c1;

TIM_HandleTypeDef htim1;
TIM_HandleTypeDef htim3;

/* USER CODE BEGIN PV */

ADC_ChannelConfTypeDef sConfigPrivate = {0};

volatile uint32_t millis_counter = 0;

/* USER CODE END PV */

void SystemClock_Config(void);
static void MX_GPIO_Init(void);
static void MX_TIM1_Init(void);
static void MX_ADC1_Init(void);
static void MX_TIM3_Init(void);
static void MX_I2C1_Init(void);
/* USER CODE BEGIN PFP */

void motor(int motor,int direction);
void speed(int Left, int Right);
void updateIR();
void calibrate();

/* USER CODE END PFP */

/* USER CODE BEGIN 0 */

#define MotorR_PWM TIM_CHANNEL_1
#define MotorL_PWM TIM_CHANNEL_2

#define Motor_RF_pin MotorR_B_Pin
#define Motor_RB_pin MotorR_A_Pin

#define Motor_RF_gpio MotorR_B_GPIO_Port
#define Motor_RB_gpio MotorR_A_GPIO_Port

#define Motor_LF_pin MotorL_B_Pin
#define Motor_LB_pin MotorL_A_Pin

#define Motor_LF_gpio MotorL_B_GPIO_Port
#define Motor_LB_gpio MotorL_A_GPIO_Port

#define left 0
#define right 1

#define Forward 1
#define Backward -1

#define Calibrate_btn GPIO_PIN_13

#define IR_ARRAY_LENGTH 9


#define MPU6050_ADDR        0xD0    // MPU6050 device address

#define REG_ACCEL_XOUT_H    0x3B    // Accelerometer X-axis data register
#define REG_GYRO_XOUT_H     0x43    // Gyroscope X-axis data register

#define REG_SMPLRT_DIV     0x19    // Gyroscope X-axis data register
#define REG_GYRO_CONFIG      0x1B    // Gyroscope X-axis data register
#define REG_ACCEL_CONFIG     0x1C   // Gyroscope X-axis data register
#define REG_TEMP_OUT_H      0x41    // Gyroscope X-axis data register
#define REG_WHO_AM_I      0x75    // Gyroscope X-axis data register
#define REG_PWR_MGMT_1      0x6B    // Gyroscope X-axis data register

I2C_HandleTypeDef hi2c1;

typedef struct {
    float Accel_X;
    float Accel_Y;
    float Accel_Z;
} MPU6050_ACCEL_t;

typedef struct {
    float Gyro_X;
    float Gyro_Y;
    float Gyro_Z;
} MPU6050_GYRO_t;


int IR_array[IR_ARRAY_LENGTH] = {0};

int button = 1;

int digital_IR[IR_ARRAY_LENGTH] = {0};

int Ir_thresholds[IR_ARRAY_LENGTH] = {2099,1840,2816,2021,1767,1914,1878,1757,2061};

// PID parameters for Line Following
double Kp = 10;
double Ki = 11;
double Kd = 7;


int Drive_constant = 200;

// Initialize PID variables
double prevError = 0;
double integral = 0;
double derivative = 0;

int verify = 0;

MPU6050_ACCEL_t accel_data;
MPU6050_GYRO_t gyro_data;

/* USER CODE END 0 */

/**
  * @brief  The application entry point.
  * @retval int
  */
int main(void)
{
  /* MCU Configuration--------------------------------------------------------*/

  /* Reset of all peripherals, Initializes the Flash interface and the Systick. */
  HAL_Init();

  /* Configure the system clock */
  SystemClock_Config();

  /* Initialize all configured peripherals */
  MX_GPIO_Init();
  MX_TIM1_Init();
  MX_ADC1_Init();
  MX_TIM3_Init();
  MX_I2C1_Init();
  /* USER CODE BEGIN 2 */

//  HAL_StatusTypeDef ret = HAL_I2C_IsDeviceReady(&hi2c1, 1101000 <<1 + 0, 1, 100);
//  if (ret == HAL_OK)
//  {
//	  verify = 3;
//  }
//  else
//  {
//	  verify = 4;
//  }

  HAL_TIM_PWM_Start(&htim1, MotorR_PWM);
  HAL_TIM_PWM_Start(&htim1, MotorL_PWM);

  HAL_TIM_Base_Start_IT(&htim3);

  HAL_ADC_Start(&hadc1);

  sConfigPrivate.Rank = ADC_REGULAR_RANK_1;
  sConfigPrivate.SamplingTime = ADC_SAMPLETIME_1CYCLE_5;

//  uint8_t temp_data = 0b00001000;
//  ret = HAL_I2C_Mem_Write(&hi2c1, (0b1101000 <<1) + 0, 27, 1, &temp_data, 1, 100);
//  if (ret == HAL_OK)
//  {
//	  verify = 7;
//  }
//  else
//  {
//	  verify = 8;
//  }


  /* USER CODE END 2 */

  /* Infinite loop */
  /* USER CODE BEGIN WHILE */
  while (1)
  {
	  MPU_Accel_Read(&accel_data);
	  MPU_Gyro_Read(&gyro_data);

	  verify = accel_data.Accel_X;
//	  speed(255,255);
//
//	  motor(left, Forward);
//	  motor(right, Backward);

//	  updateIR();
//
//	  button = HAL_GPIO_ReadPin(GPIOC,Calibrate_btn);
//
//	  if(button == RESET){
//		calibrate();
//	  }
//
////	  motor(left, Forward);
////	  motor(right, Forward);
//
//	  int array_lit_amount = 0;
//	  for (int i = 0; i < IR_ARRAY_LENGTH; i++)
//	  {
//		  array_lit_amount += digital_IR[i];
//	  }
//
//	  float left_sum = -20  * digital_IR[0] - 11 * digital_IR[1] - 6 * digital_IR[2] - 1 * digital_IR[3];
//	  float right_sum = 1 * digital_IR[5] + 6 * digital_IR[6] + 11 * digital_IR[7] + 20 * digital_IR[8];
//
//	  int position = left_sum + right_sum;
//
//	  int derivative = position - prevError;
//
//	  int PID_constant = Kp * position + Kd * derivative;
//
//	  prevError = position;
//
//	  Drive_constant = 200;
//
//	  int offset = 0; // For correcting motor speeds
//	  int Left_drive = Drive_constant + offset - PID_constant;
//	  int Right_drive = Drive_constant - offset + PID_constant;
//
//	  const int MIN_VALUE = -200;
//	  const int MAX_VALUE = 200;
//
//	  if (Left_drive < MIN_VALUE) {
//		  Left_drive = MIN_VALUE;
//	  } else if (Left_drive > MAX_VALUE) {
//		  Left_drive = MAX_VALUE;
//	  }
//
//	  if (Right_drive < MIN_VALUE) {
//		  Right_drive = MIN_VALUE;
//	  } else if (Right_drive > MAX_VALUE) {
//		  Right_drive = MAX_VALUE;
//	  }
//
//	  if(Right_drive < 0){
//		  motor(right, Backward);
//	  } else {
//		  motor(right, Forward);
//	  }
//
//
//	  if(Left_drive < 0){
//		  motor(left, Backward);
//	  } else {
//		  motor(left, Forward);
//	  }
//
//
//	  speed(abs(Left_drive), abs(Right_drive));

//	  speed(200, 200);
//
//	  motor(left, Forward);
//	  motor(right, Backward);

//	  sConfigPrivate.Channel = ADC_CHANNEL_0;
//	  HAL_ADC_ConfigChannel(&hadc1, &sConfigPrivate);
//
//	  HAL_ADC_Start(&hadc1);
//	  HAL_ADC_PollForConversion(&hadc1,1000);
//	  Digital_array[0] = HAL_ADC_GetValue(&hadc1)<3200;
//	  HAL_ADC_Stop(&hadc1);
//
//	  sConfigPrivate.Channel = ADC_CHANNEL_1;
//	  HAL_ADC_ConfigChannel(&hadc1, &sConfigPrivate);
//
//	  HAL_ADC_Start(&hadc1);
//	  HAL_ADC_PollForConversion(&hadc1,1000);
//	  Digital_array[1] = HAL_ADC_GetValue(&hadc1)<3200;
//	  HAL_ADC_Stop(&hadc1);

//	  __HAL_TIM_SET_COMPARE(&htim1, MotorR_PWM, 200);
//	  __HAL_TIM_SET_COMPARE(&htim1, MotorL_PWM, 200);
//
//	  if (Digital_array[0] == Digital_array[1]){
//		  	  // Set Right motor forward
//		  	  HAL_GPIO_WritePin(MotorR_A_GPIO_Port, MotorR_A_Pin, GPIO_PIN_RESET);
//		  	  HAL_GPIO_WritePin(MotorR_B_GPIO_Port, MotorR_B_Pin, GPIO_PIN_SET);
//
//		  	  // Set Left motor forward
//		  	  HAL_GPIO_WritePin(MotorL_A_GPIO_Port, MotorL_A_Pin, GPIO_PIN_RESET);
//		  	  HAL_GPIO_WritePin(MotorL_B_GPIO_Port, MotorL_B_Pin, GPIO_PIN_SET);
//	  }else{
//		  if(Digital_array[0] == 1){
//			  // Set Left motor forward
//			  HAL_GPIO_WritePin(MotorL_A_GPIO_Port, MotorL_A_Pin, GPIO_PIN_RESET);
//			  HAL_GPIO_WritePin(MotorL_B_GPIO_Port, MotorL_B_Pin, GPIO_PIN_RESET);
//
//			  // Set Right motor forward
//			  HAL_GPIO_WritePin(MotorR_A_GPIO_Port, MotorR_A_Pin, GPIO_PIN_RESET);
//			  HAL_GPIO_WritePin(MotorR_B_GPIO_Port, MotorR_B_Pin, GPIO_PIN_SET);
//		  } else{
//			  // Set Left motor forward
//			  HAL_GPIO_WritePin(MotorL_A_GPIO_Port, MotorL_A_Pin, GPIO_PIN_RESET);
//			  HAL_GPIO_WritePin(MotorL_B_GPIO_Port, MotorL_B_Pin, GPIO_PIN_SET);
//
//			  // Set Right motor forward
//			  HAL_GPIO_WritePin(MotorR_A_GPIO_Port, MotorR_A_Pin, GPIO_PIN_RESET);
//			  HAL_GPIO_WritePin(MotorR_B_GPIO_Port, MotorR_B_Pin, GPIO_PIN_RESET);
//
//		  }
//	  }


//	  // Set Right motor forward
//	  HAL_GPIO_WritePin(MotorR_A_GPIO_Port, MotorR_A_Pin, GPIO_PIN_SET);
//	  HAL_GPIO_WritePin(MotorR_B_GPIO_Port, MotorR_B_Pin, GPIO_PIN_RESET);
//
//	  // Set Left motor forward
//	  HAL_GPIO_WritePin(MotorL_A_GPIO_Port, MotorL_A_Pin, GPIO_PIN_SET);
//	  HAL_GPIO_WritePin(MotorL_B_GPIO_Port, MotorL_B_Pin, GPIO_PIN_RESET);
//
//	  // Change motor speed by updating TIM1 channels
//	  // Set the pulse value according to your speed requirement (between 0 to TIM1->ARR)
//	  __HAL_TIM_SET_COMPARE(&htim1, MotorR_PWM, 100);
//	  __HAL_TIM_SET_COMPARE(&htim1, MotorL_PWM, 100);
//
//	  // Delay for a while
//	  HAL_Delay(1000);
//
//	  // Set Right motor backward
//	  HAL_GPIO_WritePin(MotorR_A_GPIO_Port, MotorR_A_Pin, GPIO_PIN_RESET);
//	  HAL_GPIO_WritePin(MotorR_B_GPIO_Port, MotorR_B_Pin, GPIO_PIN_SET);
//
//	  // Set Left motor backward
//	  HAL_GPIO_WritePin(MotorL_A_GPIO_Port, MotorL_A_Pin, GPIO_PIN_RESET);
//	  HAL_GPIO_WritePin(MotorL_B_GPIO_Port, MotorL_B_Pin, GPIO_PIN_SET);
//
//	  // Change motor speed by updating TIM1 channels
//	  // Set the pulse value according to your speed requirement (between 0 to TIM1->ARR)
//	  __HAL_TIM_SET_COMPARE(&htim1, MotorR_PWM, 255);
//	  __HAL_TIM_SET_COMPARE(&htim1, MotorL_PWM, 255);
//
//	  // Delay for a while
//	  HAL_Delay(1000);
    /* USER CODE END WHILE */

    /* USER CODE BEGIN 3 */
  }
  /* USER CODE END 3 */
}

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
/* USER CODE BEGIN 4 */
void HAL_TIM_PeriodElapsedCallback(TIM_HandleTypeDef *htim) {
  if (htim->Instance == TIM3) {
    millis_counter++;
  }
}

uint32_t millis() {
  return millis_counter;
}

void speed(int Left, int Right){
	  __HAL_TIM_SET_COMPARE(&htim1,MotorR_PWM,Right);
	  __HAL_TIM_SET_COMPARE(&htim1,MotorL_PWM,Left);
}

void motor(int motor,int direction){
	if (motor == 0){
		if (direction == 1){
			HAL_GPIO_WritePin(Motor_LB_gpio, Motor_LB_pin, 0);
			HAL_GPIO_WritePin(Motor_LF_gpio, Motor_LF_pin, 1);
		}else{
			HAL_GPIO_WritePin(Motor_LB_gpio, Motor_LB_pin, 1);
			HAL_GPIO_WritePin(Motor_LF_gpio, Motor_LF_pin, 0);
		}
	}else{
		if (direction == 1){
			HAL_GPIO_WritePin(Motor_RB_gpio, Motor_RB_pin, 0);
			HAL_GPIO_WritePin(Motor_RF_gpio, Motor_RF_pin, 1);
		}else{
			HAL_GPIO_WritePin(Motor_RB_gpio, Motor_RB_pin, 1);
			HAL_GPIO_WritePin(Motor_RF_gpio, Motor_RF_pin, 0);
		}
	}
}

void calibrate()
{

//  motor(right, Backward);
//  motor(left, Forward);
//
//  // Stop motors when calibrating
//  speed(255, 255);

  // make sensor_max_values array of length IR_ARRAY_LENGTH equal to sensor calibration array
  int sensor_max_values[IR_ARRAY_LENGTH] = {0};

  // sensor min values array
  int sensor_min_values[IR_ARRAY_LENGTH] = {0};

  int now_time_for_calibration = millis();

  while (millis() - now_time_for_calibration < 5)
  {

    updateIR();
    uint8_t allZeros = 1;
    for (int i = 0; i < IR_ARRAY_LENGTH; i++)
    {
      if (sensor_max_values[i] != 0)
      {
        allZeros = 0;
        break; // No need to continue checking if we find a non-zero value
      }
    }

    if (allZeros)
    {
      for (int i = 0; i < IR_ARRAY_LENGTH; i++)
      {
        sensor_max_values[i] = IR_array[i];
        sensor_min_values[i] = IR_array[i];
      }
    }

    for (int i = 0; i < IR_ARRAY_LENGTH; i++)
    {
      if (IR_array[i] > sensor_max_values[i])
      {
        sensor_max_values[i] = IR_array[i];
      }
      if (IR_array[i] < sensor_min_values[i])
      {
        sensor_min_values[i] = IR_array[i];
      }
    }
  }

  speed(0, 0);

  for (int i = 0; i < IR_ARRAY_LENGTH; i++)
  {
    Ir_thresholds[i] = (sensor_max_values[i] + sensor_min_values[i]) / 2;
  }

}

void updateIR(){

	  sConfigPrivate.Channel = ADC_CHANNEL_0;
	  HAL_ADC_ConfigChannel(&hadc1, &sConfigPrivate);

	  HAL_ADC_Start(&hadc1);
	  HAL_ADC_PollForConversion(&hadc1,1000);
	  IR_array[0] = HAL_ADC_GetValue(&hadc1);
	  HAL_ADC_Stop(&hadc1);

	  sConfigPrivate.Channel = ADC_CHANNEL_1;
	  HAL_ADC_ConfigChannel(&hadc1, &sConfigPrivate);

	  HAL_ADC_Start(&hadc1);
	  HAL_ADC_PollForConversion(&hadc1,1000);
	  IR_array[8] = HAL_ADC_GetValue(&hadc1);
	  HAL_ADC_Stop(&hadc1);

	  sConfigPrivate.Channel = ADC_CHANNEL_2;
	  HAL_ADC_ConfigChannel(&hadc1, &sConfigPrivate);

	  HAL_ADC_Start(&hadc1);
	  HAL_ADC_PollForConversion(&hadc1,1000);
	  IR_array[1] = HAL_ADC_GetValue(&hadc1);
	  HAL_ADC_Stop(&hadc1);

	  sConfigPrivate.Channel = ADC_CHANNEL_3;
	  HAL_ADC_ConfigChannel(&hadc1, &sConfigPrivate);

	  HAL_ADC_Start(&hadc1);
	  HAL_ADC_PollForConversion(&hadc1,1000);
	  IR_array[2] = HAL_ADC_GetValue(&hadc1);
	  HAL_ADC_Stop(&hadc1);

	  sConfigPrivate.Channel = ADC_CHANNEL_4;
	  HAL_ADC_ConfigChannel(&hadc1, &sConfigPrivate);

	  HAL_ADC_Start(&hadc1);
	  HAL_ADC_PollForConversion(&hadc1,1000);
	  IR_array[3] = HAL_ADC_GetValue(&hadc1);
	  HAL_ADC_Stop(&hadc1);

	  sConfigPrivate.Channel = ADC_CHANNEL_5;
	  HAL_ADC_ConfigChannel(&hadc1, &sConfigPrivate);

	  HAL_ADC_Start(&hadc1);
	  HAL_ADC_PollForConversion(&hadc1,1000);
	  IR_array[4] = HAL_ADC_GetValue(&hadc1);
	  HAL_ADC_Stop(&hadc1);

	  sConfigPrivate.Channel = ADC_CHANNEL_6;
	  HAL_ADC_ConfigChannel(&hadc1, &sConfigPrivate);

	  HAL_ADC_Start(&hadc1);
	  HAL_ADC_PollForConversion(&hadc1,1000);
	  IR_array[5] = HAL_ADC_GetValue(&hadc1);
	  HAL_ADC_Stop(&hadc1);

	  sConfigPrivate.Channel = ADC_CHANNEL_7;
	  HAL_ADC_ConfigChannel(&hadc1, &sConfigPrivate);

	  HAL_ADC_Start(&hadc1);
	  HAL_ADC_PollForConversion(&hadc1,1000);
	  IR_array[6] = HAL_ADC_GetValue(&hadc1);
	  HAL_ADC_Stop(&hadc1);

	  sConfigPrivate.Channel = ADC_CHANNEL_10;
	  HAL_ADC_ConfigChannel(&hadc1, &sConfigPrivate);

	  HAL_ADC_Start(&hadc1);
	  HAL_ADC_PollForConversion(&hadc1,1000);
	  IR_array[7] = HAL_ADC_GetValue(&hadc1);
	  HAL_ADC_Stop(&hadc1);

	  for (int i = 0; i < 9; ++i) {
		  digital_IR[i] = IR_array[i] < Ir_thresholds[i];
	  }

}

void MPU_Accel_Read(MPU6050_ACCEL_t *Mpu_Accel)

{

        uint8_t Read_Data[6];



        HAL_I2C_Mem_Read (&hi2c1, MPU6050_ADDR, REG_ACCEL_XOUT_H, 1, Read_Data, 6, 1000);



        int16_t Accel_X_RAW = (int16_t)(Read_Data[0] << 8 | Read_Data [1]);

        int16_t Accel_Y_RAW = (int16_t)(Read_Data[2] << 8 | Read_Data [3]);

        int16_t Accel_Z_RAW = (int16_t)(Read_Data[4] << 8 | Read_Data [5]);



        Mpu_Accel -> Accel_X = (Accel_X_RAW)/16384.0;

        Mpu_Accel -> Accel_Y = (Accel_Y_RAW)/16384.0;

        Mpu_Accel -> Accel_Z = (Accel_Z_RAW)/16384.0;

}

void MPU_Gyro_Read(MPU6050_GYRO_t *Mpu_Gyro)

{

        uint8_t Read_Data[6];



        HAL_I2C_Mem_Read (&hi2c1, MPU6050_ADDR, REG_GYRO_XOUT_H, 1, Read_Data, 6, 1000);



        int16_t Gyro_X_RAW = (int16_t)(Read_Data[0] << 8 | Read_Data [1]);

        int16_t Gyro_Y_RAW = (int16_t)(Read_Data[2] << 8 | Read_Data [3]);

        int16_t Gyro_Z_RAW = (int16_t)(Read_Data[4] << 8 | Read_Data [5]);



        Mpu_Gyro -> Gyro_X = (Gyro_X_RAW)/131.0;

        Mpu_Gyro -> Gyro_Y = (Gyro_Y_RAW)/131.0;

        Mpu_Gyro -> Gyro_Z = (Gyro_Z_RAW)/131.0;

}

void MPU_Init(void)

{

uint8_t Check;

       uint8_t Data;

       HAL_I2C_Mem_Read (&hi2c1, MPU6050_ADDR, REG_WHO_AM_I, 1, &Check, 1, 1000);

      if (Check == 0x68)

     {

           Data = 0;

           HAL_I2C_Mem_Write(&hi2c1, MPU6050_ADDR, REG_PWR_MGMT_1, 1,&Data, 1, 1000);



           Data = 0x07;

           HAL_I2C_Mem_Write(&hi2c1, MPU6050_ADDR, REG_SMPLRT_DIV, 1, &Data, 1, 1000);



           Data = 0x00;

           HAL_I2C_Mem_Write(&hi2c1, MPU6050_ADDR, REG_ACCEL_CONFIG, 1, &Data, 1, 1000);



           Data = 0x00;

           HAL_I2C_Mem_Write(&hi2c1, MPU6050_ADDR, REG_GYRO_CONFIG, 1, &Data, 1, 1000);

     }

}

/* USER CODE END 4 */
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
