DinethraDivanjana2001/TechBots-STM-based-Bot-Working/STM32 firmware/SLRC ROBOT/Core/Src/main.c

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
/* Includes ------------------------------------------------------------------*/
#include "main.h"

/* USER CODE BEGIN Includes */
#include "TPS55288.h"
#include "stm32f4xx_hal.h"
/* USER CODE END Includes */

ADC_HandleTypeDef hadc1;
ADC_HandleTypeDef hadc2;

I2C_HandleTypeDef hi2c2;

SPI_HandleTypeDef hspi1;

TIM_HandleTypeDef htim1;
TIM_HandleTypeDef htim2;
TIM_HandleTypeDef htim3;
TIM_HandleTypeDef htim4;
TIM_HandleTypeDef htim6;
TIM_HandleTypeDef htim8;
TIM_HandleTypeDef htim9;

UART_HandleTypeDef huart4;

/* USER CODE BEGIN PV */
//TPS55288 BuckBoost;
volatile uint32_t millis_counter = 0;
HAL_StatusTypeDef result;
HAL_StatusTypeDef result1;
HAL_StatusTypeDef result2;
HAL_StatusTypeDef IDR_Result;
uint8_t errors = 0;
uint8_t array_no = 0;
int pid_sum = 0;
float pid_sum1 = 0;
uint8_t I2C_Address = 0;
uint8_t TX_Buffer [] = "A" ; // DATA to send
ADC_ChannelConfTypeDef adc1ConfigPrivate = {0};
ADC_ChannelConfTypeDef adc2ConfigPrivate = {0};


/* USER CODE END PV */

void SystemClock_Config(void);
static void MX_GPIO_Init(void);
static void MX_ADC1_Init(void);
static void MX_I2C2_Init(void);
static void MX_TIM1_Init(void);
static void MX_TIM3_Init(void);
static void MX_TIM4_Init(void);
static void MX_TIM8_Init(void);
static void MX_TIM9_Init(void);
static void MX_UART4_Init(void);
static void MX_SPI1_Init(void);
static void MX_ADC2_Init(void);
static void MX_TIM2_Init(void);
static void MX_TIM6_Init(void);
/* USER CODE BEGIN PFP */
void motor(int motor,int direction);
void speed(int Left, int Right);
void updateIR();
void calibrate();
void FR_Array_Mux_In_Select(int IR_LED_Num);


/* USER CODE END PFP */

/* USER CODE BEGIN 0 */
#define TCS3472_ADDRESS 0x29 // I2C address of the TCS3472 device

#define left 0
#define right 1

#define Forward 1
#define Backward -1

#define RR_MOTOR_PWM TIM_CHANNEL_1
#define FR_MOTOR_PWM TIM_CHANNEL_2

#define IR_ARRAY_LENGTH 25

int IR_array[IR_ARRAY_LENGTH] = {0};

int digital_IR[IR_ARRAY_LENGTH] = {0};

int Ir_thresholds[IR_ARRAY_LENGTH] = {2099,1840,2816,2021,1767,1914,1878,1757,2099,1840,2816,2021,1767,1914,1878,1757,2099,1840,2816,2021,1767,1914,1878,1757,1800};

uint8_t FR_IR_LED_ARR[25][5] = {
	{0,0,0,0,0},//Y0 IR1
	{0,0,0,0,1},//Y1 IR2
	{0,0,0,1,0},//Y2 IR3
	{0,0,0,1,1},//Y3 IR4
	{0,0,1,0,0},//Y4 IR5
	{0,0,1,0,1},//Y5 IR6
	{0,0,1,1,0},//Y6 IR7
	{0,0,1,1,1},//Y7 IR8
	{0,1,1,1,1},//Y15 IR9
	{0,1,1,1,0},//Y14 IR10
	{0,1,1,0,1},//Y13 IR11
	{0,1,1,0,0},//Y12 IR12
	{0,1,0,1,1},//Y11 IR13
	{0,1,0,1,0},//Y10 IR14
	{0,1,0,0,1},//Y9 IR15
	{0,1,0,0,0},//Y8 IR16
	{1,0,0,0,0},//Y0 IR17
	{1,0,0,0,1},//Y1 IR18
	{1,0,0,1,0},//Y2 IR19
	{1,0,0,1,1},//Y3 IR20
	{1,0,1,0,0},//Y4 IR21
	{1,0,1,0,1},//Y5 IR22
	{1,0,1,1,0},//Y6 IR23
	{1,0,1,1,1},//Y7 IR24
	{1,1,0,0,0}};//Y8 IR25

// PID parameters for Line Following
double Kp = 0.02;
double Ki = 11;
double Kd = 0.1;


int Drive_constant = 500;

// Initialize PID variables
double prevError = 0;
double integral = 0;
double derivative = 0;
/* USER CODE END 0 */

/**
  * @brief  The application entry point.
  * @retval int
  */
int main(void)
{
  /* MCU Configuration--------------------------------------------------------*/

  /* Reset of all peripherals, Initializes the Flash interface and the Systick. */
  HAL_Init();

  /* Configure the system clock */
  SystemClock_Config();

  /* Initialize all configured peripherals */
  MX_GPIO_Init();
  MX_ADC1_Init();
  MX_I2C2_Init();
  MX_TIM1_Init();
  MX_TIM3_Init();
  MX_TIM4_Init();
  MX_TIM8_Init();
  MX_TIM9_Init();
  MX_UART4_Init();
  MX_SPI1_Init();
  MX_ADC2_Init();
  MX_TIM2_Init();
  MX_TIM6_Init();
  /* USER CODE BEGIN 2 */

  HAL_TIM_PWM_Start(&htim1, TIM_CHANNEL_1);
  HAL_TIM_PWM_Start(&htim1, TIM_CHANNEL_2);
  HAL_TIM_Base_Start_IT(&htim3);


  /* USER CODE END 2 */

  /* Infinite loop */
  /* USER CODE BEGIN WHILE */
  while (1)
  {
    /* USER CODE END WHILE */

    /* USER CODE BEGIN 3 */


//	  result =HAL_I2C_Mem_Write(&hi2c2,TPS55288_I2C_ADDR,command,1,&config, 1 ,10); //Sending in Blocking mode
 // for the return value from HAL function calls
//	  result =HAL_I2C_Mem_Write(&hi2c2, (E0 << 1), 0x06, I2C_MEMADD_SIZE_8BIT, 0xA0, 1, 10);
//
//
//	  if(result == HAL_ERROR){
//		  errors=errors+1;
//
//	  }
//	  if(result1 == HAL_ERROR){
//		  errors=errors+1;
//
//	  }
//	  if(result2 == HAL_ERROR){
//		  errors=errors+1;
//
//	  }



//		  HAL_GPIO_WritePin(CLR_LED_3_GPIO_Port, CLR_LED_3_Pin, GPIO_PIN_RESET);



	  /* USER CODE END WHILE */

	  /* USER CODE BEGIN 3 */

//	 for(uint8_t counter = 0 ; counter < 255; counter++){
//
//	 IDR_Result = HAL_I2C_IsDeviceReady(&hi2c2, (0x70 << 1), 3, 10);
////
//	 if(IDR_Result == HAL_OK){
//
//	 I2C_Address = I2C_Address+1;
//
////	 HAL_GPIO_TogglePin(GPIOG, GPIO_PIN_14);
//
//	 }

//	 }

//	 HAL_GPIO_TogglePin(GPIOG, GPIO_PIN_13);

//	 HAL_Delay(500);


//	  result1 =HAL_I2C_Mem_Write( &hi2c2, TPS55288_I2C_ADDR, TPS55288_VOUT_FS, I2C_MEMADD_SIZE_8BIT, 0x83, 1, HAL_MAX_DELAY);

//	  result1 =HAL_I2C_Mem_Write( &hi2c2, TPS55288_I2C_ADDR, TPS55288_IOUT_LIMIT, I2C_MEMADD_SIZE_8BIT, 0x64, 1, HAL_MAX_DELAY);

//		result = HAL_I2C_IsDeviceReady( &hi2c2, 0x74<<1, 10, 1000 );
//	  HAL_Delay(100);
//	  HAL_GPIO_WritePin(FR_ARRAY_EVEN_GPIO_Port, FR_ARRAY_EVEN_Pin, GPIO_PIN_SET);
//	  HAL_GPIO_WritePin(FR_ARRAY_ODD_GPIO_Port, FR_ARRAY_ODD_Pin, GPIO_PIN_RESET);
//	  HAL_Delay(1500);
//	  HAL_GPIO_WritePin(FR_ARRAY_ODD_GPIO_Port, FR_ARRAY_ODD_Pin, GPIO_PIN_SET);
//	  HAL_GPIO_WritePin(FR_ARRAY_EVEN_GPIO_Port, FR_ARRAY_EVEN_Pin, GPIO_PIN_RESET);
//	  HAL_Delay(1500);

//	 	  motor(left, Backward);
//	 	  motor(right, Backward);

	 	  updateIR();

	 	  int array_lit_amount = 0;
	 	  for (int i = 0; i < IR_ARRAY_LENGTH; i++)
	 	  {
	 		  array_lit_amount += digital_IR[i];
	 	  }

	 	  int left_sum =  4400  * digital_IR[0] + 4000 * digital_IR[1] + 3600 * digital_IR[2] + 3200 * digital_IR[3] + 2980  * digital_IR[4] + 1096 * digital_IR[5] + 403 * digital_IR[6] + 148 * digital_IR[7] + 54 * digital_IR[8] + 20 * digital_IR[9] + 8  * digital_IR[10] + 3 * digital_IR[11];
	 	  int right_sum = 3  * digital_IR[13] + 8 * digital_IR[14] + 20 * digital_IR[15] + 54 * digital_IR[16] + 148  * digital_IR[17] + 403 * digital_IR[18] + 1096 * digital_IR[19] + 2980 * digital_IR[20] + 3200 * digital_IR[21] + 3600 * digital_IR[22] + 4000 * digital_IR[23] + 4400 * digital_IR[24];


	 	  int position =  right_sum  - left_sum ;


	 	  int derivative = position - prevError;

	 	  float PID_constant = Kp * position + Kd * derivative;

	 	  prevError = position;

	 	  Drive_constant = 400;

	 	  float offset = 0; // For correcting motor speeds
	 	  int Left_drive = Drive_constant + offset  - PID_constant;
	 	  int Right_drive = Drive_constant - offset + PID_constant;
	 	  pid_sum = Left_drive;
	 	 pid_sum1 = PID_constant;
	 	  const int MIN_VALUE = -1024;
	 	  const int MAX_VALUE = 1024;

	 	  if (Left_drive < MIN_VALUE) {
	 		  Left_drive = MIN_VALUE;
	 	  } else if (Left_drive > MAX_VALUE) {
	 		  Left_drive = MAX_VALUE;
	 	  }

	 	  if (Right_drive < MIN_VALUE) {
	 		  Right_drive = MIN_VALUE;
	 	  } else if (Right_drive > MAX_VALUE) {
	 		  Right_drive = MAX_VALUE;
	 	  }

	 	  if(Right_drive < 0){
	 		  motor(right, Backward);
	 	  } else {
	 		  motor(right, Forward);
	 	  }


	 	  if(Left_drive < 0){
	 		  motor(left, Backward);
	 	  } else {
	 		  motor(left, Forward);
	 	  }


	 	  speed(Left_drive, Right_drive);
//	 	 speed(500, 500);
	 //	 servo_sweep();
	 //
	 //	 // Read color data
	 //	 TCS3472_Read_Color_Data(&hi2c2, &clear, &red, &green, &blue);
	 //
	 //	 // Use the color data as needed
	 //	 // Example: Print the values
	 //	 printf("Clear: %u, Red: %u, Green: %u, Blue: %u\n", clear, red, green, blue);
	 //
	 //	 // Delay or perform other operations
	 //	 HAL_Delay(1000); // Delay for 1 second



  }
  /* USER CODE END 3 */
}

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
/* USER CODE BEGIN 4 */

void HAL_TIM_PeriodElapsedCallback(TIM_HandleTypeDef *htim) {
  if (htim->Instance == TIM6) {
    millis_counter++;
  }
}

uint32_t millis() {
  return millis_counter;
}

void speed(int Left, int Right){
	  __HAL_TIM_SET_COMPARE(&htim1,FR_MOTOR_PWM,Right);
	  __HAL_TIM_SET_COMPARE(&htim1,RR_MOTOR_PWM,Left);
}

void motor(int motor,int direction){
	if (motor == 0){
		if (direction == 1){
			HAL_GPIO_WritePin(RR_INB_GPIO_Port, RR_INB_Pin, 1);
			HAL_GPIO_WritePin(RR_INA_GPIO_Port, RR_INA_Pin, 0);
		}else{
			HAL_GPIO_WritePin(RR_INB_GPIO_Port, RR_INB_Pin, 0);
			HAL_GPIO_WritePin(RR_INA_GPIO_Port, RR_INA_Pin, 1);
		}
	}else{
		if (direction == 1){
			HAL_GPIO_WritePin(FR_INB_GPIO_Port, FR_INB_Pin, 0);
			HAL_GPIO_WritePin(FR_INA_GPIO_Port, FR_INA_Pin, 1);
		}else{
			HAL_GPIO_WritePin(FR_INB_GPIO_Port, FR_INB_Pin, 1);
			HAL_GPIO_WritePin(FR_INA_GPIO_Port, FR_INA_Pin, 0);
		}
	}
}

void updateIR(){
	  // loop through amount of leds. ARRAY STARTS FROM 1
	   HAL_GPIO_WritePin(FR_ARRAY_EVEN_GPIO_Port, FR_ARRAY_EVEN_Pin, GPIO_PIN_SET);
	 	HAL_GPIO_WritePin(FR_ARRAY_ODD_GPIO_Port, FR_ARRAY_ODD_Pin, GPIO_PIN_SET);
	  for (int i = 0; i < 25; i=i+2) {
		  array_no = i;
			FR_Array_Mux_In_Select(i+1);
		  if(i <= 15){
	  		  	adc1ConfigPrivate.Channel = ADC_CHANNEL_10;
	  		  	HAL_ADC_ConfigChannel(&hadc1, &adc1ConfigPrivate);
	  		    HAL_ADC_Start(&hadc1);
	  		    HAL_ADC_PollForConversion(&hadc1, HAL_MAX_DELAY);
//	  		    raw = HAL_ADC_GetValue(&hadc1);
	  		    IR_array[i] = HAL_ADC_GetValue(&hadc1);
//		  			delay_us(2);

		  }else{
			adc2ConfigPrivate.Channel = ADC_CHANNEL_11;
	  		  	HAL_ADC_ConfigChannel(&hadc2, &adc2ConfigPrivate);
	  		    HAL_ADC_Start(&hadc2);
	  		    HAL_ADC_PollForConversion(&hadc2, HAL_MAX_DELAY);
//	  		    raw = HAL_ADC_GetValue(&hadc2);
	  		    IR_array[i] = HAL_ADC_GetValue(&hadc2);
//		  			delay_us(2);
		  }
		  digital_IR[i] = IR_array[i] < Ir_thresholds[i];
		  HAL_Delay(1);
	  }
	  for (int i = 1; i < 25; i=i+2) {
		  array_no = i;
			FR_Array_Mux_In_Select(i+1);
		  if(i <= 15){
	  		  	adc1ConfigPrivate.Channel = ADC_CHANNEL_10;
	  		  	HAL_ADC_ConfigChannel(&hadc1, &adc1ConfigPrivate);
	  		    HAL_ADC_Start(&hadc1);
	  		    HAL_ADC_PollForConversion(&hadc1, HAL_MAX_DELAY);
//	  		    raw = HAL_ADC_GetValue(&hadc1);
	  		    IR_array[i] = HAL_ADC_GetValue(&hadc1);
//		  			delay_us(2);
		  }else{
			adc2ConfigPrivate.Channel = ADC_CHANNEL_11;
	  		  	HAL_ADC_ConfigChannel(&hadc2, &adc2ConfigPrivate);
	  		    HAL_ADC_Start(&hadc2);
	  		    HAL_ADC_PollForConversion(&hadc2, HAL_MAX_DELAY);
//	  		    raw = HAL_ADC_GetValue(&hadc2);
	  		    IR_array[i] = HAL_ADC_GetValue(&hadc2);
//		  			delay_us(2);

		  }
		  digital_IR[i] = IR_array[i] < Ir_thresholds[i];
		  HAL_Delay(1);
	  }
}


void FR_Array_Mux_In_Select(int IR_LED_Num){
	if(IR_LED_Num <= 16){
	    HAL_GPIO_WritePin(FR_ARRAY_SA0_GPIO_Port, FR_ARRAY_SA0_Pin, FR_IR_LED_ARR[IR_LED_Num-1][4]);
	    HAL_GPIO_WritePin(FR_ARRAY_SA1_GPIO_Port, FR_ARRAY_SA1_Pin, FR_IR_LED_ARR[IR_LED_Num-1][3]);
	    HAL_GPIO_WritePin(FR_ARRAY_SA2_GPIO_Port, FR_ARRAY_SA2_Pin, FR_IR_LED_ARR[IR_LED_Num-1][2]);
	    HAL_GPIO_WritePin(FR_ARRAY_SA3_GPIO_Port, FR_ARRAY_SA3_Pin, FR_IR_LED_ARR[IR_LED_Num-1][1]);
	}	if(IR_LED_Num > 16){
	    HAL_GPIO_WritePin(FR_ARRAY_SB0_GPIO_Port, FR_ARRAY_SB0_Pin, FR_IR_LED_ARR[IR_LED_Num-1][4]);
	    HAL_GPIO_WritePin(FR_ARRAY_SB1_GPIO_Port, FR_ARRAY_SB1_Pin, FR_IR_LED_ARR[IR_LED_Num-1][3]);
	    HAL_GPIO_WritePin(FR_ARRAY_SB2_GPIO_Port, FR_ARRAY_SB2_Pin, FR_IR_LED_ARR[IR_LED_Num-1][2]);
	    HAL_GPIO_WritePin(FR_ARRAY_SB3_GPIO_Port, FR_ARRAY_SB3_Pin, FR_IR_LED_ARR[IR_LED_Num-1][1]);
	}

}

void calibrate()
{

//  motor(right, Backward);
//  motor(left, Forward);
//
//  // Stop motors when calibrating
//  speed(255, 255);

  // make sensor_max_values array of length IR_ARRAY_LENGTH equal to sensor calibration array
  int sensor_max_values[IR_ARRAY_LENGTH] = {0};

  // sensor min values array
  int sensor_min_values[IR_ARRAY_LENGTH] = {0};

  int now_time_for_calibration = millis();

  while (millis() - now_time_for_calibration < 5)
  {

    updateIR();
    uint8_t allZeros = 1;
    for (int i = 0; i < IR_ARRAY_LENGTH; i++)
    {
      if (sensor_max_values[i] != 0)
      {
        allZeros = 0;
        break; // No need to continue checking if we find a non-zero value
      }
    }

    if (allZeros)
    {
      for (int i = 0; i < IR_ARRAY_LENGTH; i++)
      {
        sensor_max_values[i] = IR_array[i];
        sensor_min_values[i] = IR_array[i];
      }
    }

    for (int i = 0; i < IR_ARRAY_LENGTH; i++)
    {
      if (IR_array[i] > sensor_max_values[i])
      {
        sensor_max_values[i] = IR_array[i];
      }
      if (IR_array[i] < sensor_min_values[i])
      {
        sensor_min_values[i] = IR_array[i];
      }
    }
  }

  speed(0, 0);

  for (int i = 0; i < IR_ARRAY_LENGTH; i++)
  {
    Ir_thresholds[i] = (sensor_max_values[i] + sensor_min_values[i]) / 2;
  }

}

//// EXTI line 1 interrupt handler
//void EXTI0_IRQHandler(void) {
//    // Your code here
//    // This code will be executed when the interrupt occurs
//    // Handle the interrupt (e.g., clear the interrupt flag)
//    HAL_GPIO_EXTI_IRQHandler(CLR_INT_2_Pin); // Assuming GPIO_PIN_1 is the pin associated with EXTI line 1
//}

void servo_sweep(void){
	int x;
	  for(x=1400; x<7000; x=x+1)
	  {
		__HAL_TIM_SET_COMPARE(&htim8,TIM_CHANNEL_1, x);
		HAL_Delay(3);
	  }

	  for(x=1400; x<7000; x=x+1)
	  {
		__HAL_TIM_SET_COMPARE(&htim8,TIM_CHANNEL_2, x);
		HAL_Delay(3);
	  }

	  for(x=1400; x<7000; x=x+1)
	  {
		__HAL_TIM_SET_COMPARE(&htim8,TIM_CHANNEL_3, x);
		HAL_Delay(3);
	  }

	  for(x=1400; x<7000; x=x+1)
	  {
		__HAL_TIM_SET_COMPARE(&htim8,TIM_CHANNEL_4, x);
		HAL_Delay(3);
	  }
}

//// Function to initialize TCS3472
//void TCS3472_Init(I2C_HandleTypeDef *hi2c) {
//    // Example initialization steps
//    // Write to the command register to set up the device
//    // You may need to set integration time, wait time, etc.
//    // Refer to the datasheet for initialization details
//}
//
//// Function to read color data from TCS3472
//void TCS3472_Read_Color_Data(I2C_HandleTypeDef *hi2c, uint16_t *clear, uint16_t *red, uint16_t *green, uint16_t *blue) {
//    // Write to the command register to select the desired register for reading color data
//    // For example, to read clear data, you need to write the command register with 0x14 address
//    uint8_t command = 0x14;
//    HAL_I2C_Master_Transmit(hi2c, TCS3472_ADDRESS << 1, &command, 1, HAL_MAX_DELAY);
//
//    // Read color data
//    uint8_t data[8]; // Assuming each color data is 2 bytes
//    HAL_I2C_Master_Receive(hi2c, TCS3472_ADDRESS << 1, data, 8, HAL_MAX_DELAY);
//
//    // Extract color data from received data
//    *clear = (data[1] << 8) | data[0]; // Assuming clear data is in register 0x14
//    *red = (data[3] << 8) | data[2];   // Assuming red data is in register 0x16
//    *green = (data[5] << 8) | data[4]; // Assuming green data is in register 0x18
//    *blue = (data[7] << 8) | data[6];  // Assuming blue data is in register 0x1A
//}



//int computeSum(int side, int* IR_ARRAY, int* CONSTANT_ARRAY) {
//	if(side == "RH"){
//	    int sum = 0;
//	    for (int i = 0; i < CONSTANT_ARRAY_LENGTH; ++i) {
//	        sum += IR_ARRAY[i] * CONSTANT_ARRAY[i];
//	    }
//	    return sum;
//
//	}
//	else if(side == "LH"){
//	    int sum = 0;
//	    for (int i = 0; i < CONSTANT_ARRAY_LENGTH; ++i) {
//	        sum += IR_ARRAY[i+CONSTANT_ARRAY_LENGTH+1] * CONSTANT_ARRAY[i];
//	    }
//	    return sum;
//	}
//
//}
/* USER CODE END 4 */
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
