DinethraDivanjana2001/TechBots-STM-based-Bot-Working/STM32 firmware/SLRC ROBOT_main/Core/Inc/mpu6050.h

#ifndef INC_MPU6050_H_
#define INC_MPU6050_H_

#define DEVICE_ADDRESS 0x68
#define FS_GYRO_250    0
#define FS_GYRO_500    8
#define FS_GYRO_1000   9
#define FS_GYRO_2000   10

#define FS_ACC_2G      0
#define FS_ACC_4G      8
#define FS_ACC_8G      9
#define FS_ACC_16G     10

#define REG_CONFIG_GYRO   27
#define REG_CONFIG_ACC    28
#define REG_USR_CTRL     107
#define GYRO_Z         71

void mpu6050_int();
int mpu6050_read();

#endif / INC_MPU6050_H_ */
